Hugh-rymcu/BigSmart-Open/site/pnpm-lock.yaml

lockfileVersion: '9.0'

settings:
  autoInstallPeers: true
  excludeLinksFromLockfile: false

importers:

  .:
    dependencies:
      '@iconify-json/lucide':
        specifier: ^1.2.106
        version: 1.2.106
      '@iconify-json/simple-icons':
        specifier: ^1.2.81
        version: 1.2.81
      '@iconify-json/vscode-icons':
        specifier: ^1.2.49
        version: 1.2.49
      '@nuxt/content':
        specifier: ^3.13.0
        version: 3.13.0(better-sqlite3@12.9.0)(magicast@0.5.2)
      '@nuxt/image':
        specifier: ^2.0.0
        version: 2.0.0(db0@0.3.4(better-sqlite3@12.9.0))(ioredis@5.10.1)(magicast@0.5.2)
      '@nuxt/ui':
        specifier: ^4.7.1
        version: 4.7.1(@internationalized/date@3.12.0)(@internationalized/number@3.6.5)(@nuxt/content@3.13.0(better-sqlite3@12.9.0)(magicast@0.5.2))(@tiptap/extensions@3.22.4(@tiptap/core@3.22.4(@tiptap/pm@3.22.4))(@tiptap/pm@3.22.4))(@tiptap/y-tiptap@3.0.2(prosemirror-model@1.25.4)(prosemirror-state@1.4.4)(prosemirror-view@1.41.6)(y-protocols@1.0.7(yjs@13.6.30))(yjs@13.6.30))(change-case@5.4.4)(db0@0.3.4(better-sqlite3@12.9.0))(embla-carousel@8.6.0)(ioredis@5.10.1)(magicast@0.5.2)(tailwindcss@4.3.0)(typescript@6.0.3)(vite@7.3.2(@types/node@25.5.0)(jiti@2.6.1)(lightningcss@1.32.0)(terser@5.46.1)(yaml@2.8.2))(vue-router@5.0.6(@vue/compiler-sfc@3.5.33)(vue@3.5.33(typescript@6.0.3)))(vue@3.5.33(typescript@6.0.3))(yjs@13.6.30)(zod@4.4.3)
      '@nuxtjs/mcp-toolkit':
        specifier: ^0.16.1
        version: 0.16.1(@vue/compiler-sfc@3.5.33)(h3@1.15.11)(magicast@0.5.2)(rollup@4.60.2)(vite@7.3.2(@types/node@25.5.0)(jiti@2.6.1)(lightningcss@1.32.0)(terser@5.46.1)(yaml@2.8.2))(vue@3.5.33(typescript@6.0.3))(zod@4.4.3)
      '@nuxtjs/mdc':
        specifier: ^0.21.1
        version: 0.21.1(magicast@0.5.2)
      '@vueuse/core':
        specifier: ^14.3.0
        version: 14.3.0(vue@3.5.33(typescript@6.0.3))
      minimark:
        specifier: ^0.2.0
        version: 0.2.0
      nuxt:
        specifier: ^4.4.5
        version: 4.4.5(@babel/core@7.29.0)(@babel/plugin-syntax-jsx@7.28.6(@babel/core@7.29.0))(@parcel/watcher@2.5.6)(@types/node@25.5.0)(@vue/compiler-sfc@3.5.33)(better-sqlite3@12.9.0)(cac@6.7.14)(db0@0.3.4(better-sqlite3@12.9.0))(eslint@10.3.0(jiti@2.6.1))(ioredis@5.10.1)(lightningcss@1.32.0)(magicast@0.5.2)(optionator@0.9.4)(rollup-plugin-visualizer@7.0.1(rollup@4.60.2))(rollup@4.60.2)(terser@5.46.1)(typescript@6.0.3)(vite@7.3.2(@types/node@25.5.0)(jiti@2.6.1)(lightningcss@1.32.0)(terser@5.46.1)(yaml@2.8.2))(vue-tsc@3.2.8(typescript@6.0.3))(yaml@2.8.2)
      nuxt-llms:
        specifier: 0.2.0
        version: 0.2.0(magicast@0.5.2)
      tailwindcss:
        specifier: ^4.3.0
        version: 4.3.0
      ufo:
        specifier: ^1.6.4
        version: 1.6.4
      unist-util-visit:
        specifier: ^5.1.0
        version: 5.1.0
      zod:
        specifier: ^4.4.3
        version: 4.4.3
    devDependencies:
      '@nuxt/eslint':
        specifier: ^1.15.2
        version: 1.15.2(@typescript-eslint/utils@8.57.0(eslint@10.3.0(jiti@2.6.1))(typescript@6.0.3))(@vue/compiler-sfc@3.5.33)(eslint@10.3.0(jiti@2.6.1))(magicast@0.5.2)(typescript@6.0.3)(vite@7.3.2(@types/node@25.5.0)(jiti@2.6.1)(lightningcss@1.32.0)(terser@5.46.1)(yaml@2.8.2))
      eslint:
        specifier: ^10.3.0
        version: 10.3.0(jiti@2.6.1)
      typescript:
        specifier: ^6.0.3
        version: 6.0.3
      vue-tsc:
        specifier: ^3.2.8
        version: 3.2.8(typescript@6.0.3)

packages:

  '@alloc/quick-lru@5.2.0':
    resolution: {integrity: sha512-UrcABB+4bUrFABwbluTIBErXwvbsU/V7TZWfmbgJfbkwiBuziS9gxdODUyuiecfdGQ85jglMW6juS3+z5TsKLw==}
    engines: {node: '>=10'}

  '@antfu/install-pkg@1.1.0':
    resolution: {integrity: sha512-MGQsmw10ZyI+EJo45CdSER4zEb+p31LpDAFp2Z3gkSd1yqVZGi0Ebx++YTEMonJy4oChEMLsxZ64j8FH6sSqtQ==}

  '@apidevtools/json-schema-ref-parser@14.2.1':
    resolution: {integrity: sha512-HmdFw9CDYqM6B25pqGBpNeLCKvGPlIx1EbLrVL0zPvj50CJQUHyBNBw45Muk0kEIkogo1VZvOKHajdMuAzSxRg==}
    engines: {node: '>= 20'}
    peerDependencies:
      '@types/json-schema': ^7.0.15

  '@babel/code-frame@7.29.0':
    resolution: {integrity: sha512-9NhCeYjq9+3uxgdtp20LSiJXJvN0FeCtNGpJxuMFZ1Kv3cWUNb6DOhJwUvcVCzKGR66cw4njwM6hrJLqgOwbcw==}
    engines: {node: '>=6.9.0'}

  '@babel/compat-data@7.29.0':
    resolution: {integrity: sha512-T1NCJqT/j9+cn8fvkt7jtwbLBfLC/1y1c7NtCeXFRgzGTsafi68MRv8yzkYSapBnFA6L3U2VSc02ciDzoAJhJg==}
    engines: {node: '>=6.9.0'}

  '@babel/core@7.29.0':
    resolution: {integrity: sha512-CGOfOJqWjg2qW/Mb6zNsDm+u5vFQ8DxXfbM09z69p5Z6+mE1ikP2jUXw+j42Pf1XTYED2Rni5f95npYeuwMDQA==}
    engines: {node: '>=6.9.0'}

  '@babel/generator@7.29.1':
    resolution: {integrity: sha512-qsaF+9Qcm2Qv8SRIMMscAvG4O3lJ0F1GuMo5HR/Bp02LopNgnZBC/EkbevHFeGs4ls/oPz9v+Bsmzbkbe+0dUw==}
    engines: {node: '>=6.9.0'}

  '@babel/helper-annotate-as-pure@7.27.3':
    resolution: {integrity: sha512-fXSwMQqitTGeHLBC08Eq5yXz2m37E4pJX1qAU1+2cNedz/ifv/bVXft90VeSav5nFO61EcNgwr0aJxbyPaWBPg==}
    engines: {node: '>=6.9.0'}

  '@babel/helper-compilation-targets@7.28.6':
    resolution: {integrity: sha512-JYtls3hqi15fcx5GaSNL7SCTJ2MNmjrkHXg4FSpOA/grxK8KwyZ5bubHsCq8FXCkua6xhuaaBit+3b7+VZRfcA==}
    engines: {node: '>=6.9.0'}

  '@babel/helper-create-class-features-plugin@7.28.6':
    resolution: {integrity: sha512-dTOdvsjnG3xNT9Y0AUg1wAl38y+4Rl4sf9caSQZOXdNqVn+H+HbbJ4IyyHaIqNR6SW9oJpA/RuRjsjCw2IdIow==}
    engines: {node: '>=6.9.0'}
    peerDependencies:
      '@babel/core': ^7.0.0

  '@babel/helper-globals@7.28.0':
    resolution: {integrity: sha512-+W6cISkXFa1jXsDEdYA8HeevQT/FULhxzR99pxphltZcVaugps53THCeiWA8SguxxpSp3gKPiuYfSWopkLQ4hw==}
    engines: {node: '>=6.9.0'}

  '@babel/helper-member-expression-to-functions@7.28.5':
    resolution: {integrity: sha512-cwM7SBRZcPCLgl8a7cY0soT1SptSzAlMH39vwiRpOQkJlh53r5hdHwLSCZpQdVLT39sZt+CRpNwYG4Y2v77atg==}
    engines: {node: '>=6.9.0'}

  '@babel/helper-module-imports@7.28.6':
    resolution: {integrity: sha512-l5XkZK7r7wa9LucGw9LwZyyCUscb4x37JWTPz7swwFE/0FMQAGpiWUZn8u9DzkSBWEcK25jmvubfpw2dnAMdbw==}
    engines: {node: '>=6.9.0'}

  '@babel/helper-module-transforms@7.28.6':
    resolution: {integrity: sha512-67oXFAYr2cDLDVGLXTEABjdBJZ6drElUSI7WKp70NrpyISso3plG9SAGEF6y7zbha/wOzUByWWTJvEDVNIUGcA==}
    engines: {node: '>=6.9.0'}
    peerDependencies:
      '@babel/core': ^7.0.0

  '@babel/helper-optimise-call-expression@7.27.1':
    resolution: {integrity: sha512-URMGH08NzYFhubNSGJrpUEphGKQwMQYBySzat5cAByY1/YgIRkULnIy3tAMeszlL/so2HbeilYloUmSpd7GdVw==}
    engines: {node: '>=6.9.0'}

  '@babel/helper-plugin-utils@7.28.6':
    resolution: {integrity: sha512-S9gzZ/bz83GRysI7gAD4wPT/AI3uCnY+9xn+Mx/KPs2JwHJIz1W8PZkg2cqyt3RNOBM8ejcXhV6y8Og7ly/Dug==}
    engines: {node: '>=6.9.0'}

  '@babel/helper-replace-supers@7.28.6':
    resolution: {integrity: sha512-mq8e+laIk94/yFec3DxSjCRD2Z0TAjhVbEJY3UQrlwVo15Lmt7C2wAUbK4bjnTs4APkwsYLTahXRraQXhb1WCg==}
    engines: {node: '>=6.9.0'}
    peerDependencies:
      '@babel/core': ^7.0.0

  '@babel/helper-skip-transparent-expression-wrappers@7.27.1':
    resolution: {integrity: sha512-Tub4ZKEXqbPjXgWLl2+3JpQAYBJ8+ikpQ2Ocj/q/r0LwE3UhENh7EUabyHjz2kCEsrRY83ew2DQdHluuiDQFzg==}
    engines: {node: '>=6.9.0'}

  '@babel/helper-string-parser@7.27.1':
    resolution: {integrity: sha512-qMlSxKbpRlAridDExk92nSobyDdpPijUq2DW6oDnUqd0iOGxmQjyqhMIihI9+zv4LPyZdRje2cavWPbCbWm3eA==}
    engines: {node: '>=6.9.0'}

  '@babel/helper-validator-identifier@7.28.5':
    resolution: {integrity: sha512-qSs4ifwzKJSV39ucNjsvc6WVHs6b7S03sOh2OcHF9UHfVPqWWALUsNUVzhSBiItjRZoLHx7nIarVjqKVusUZ1Q==}
    engines: {node: '>=6.9.0'}

  '@babel/helper-validator-option@7.27.1':
    resolution: {integrity: sha512-YvjJow9FxbhFFKDSuFnVCe2WxXk1zWc22fFePVNEaWJEu8IrZVlda6N0uHwzZrUM1il7NC9Mlp4MaJYbYd9JSg==}
    engines: {node: '>=6.9.0'}

  '@babel/helpers@7.28.6':
    resolution: {integrity: sha512-xOBvwq86HHdB7WUDTfKfT/Vuxh7gElQ+Sfti2Cy6yIWNW05P8iUslOVcZ4/sKbE+/jQaukQAdz/gf3724kYdqw==}
    engines: {node: '>=6.9.0'}

  '@babel/parser@7.29.2':
    resolution: {integrity: sha512-4GgRzy/+fsBa72/RZVJmGKPmZu9Byn8o4MoLpmNe1m8ZfYnz5emHLQz3U4gLud6Zwl0RZIcgiLD7Uq7ySFuDLA==}
    engines: {node: '>=6.0.0'}
    hasBin: true

  '@babel/plugin-syntax-jsx@7.28.6':
    resolution: {integrity: sha512-wgEmr06G6sIpqr8YDwA2dSRTE3bJ+V0IfpzfSY3Lfgd7YWOaAdlykvJi13ZKBt8cZHfgH1IXN+CL656W3uUa4w==}
    engines: {node: '>=6.9.0'}
    peerDependencies:
      '@babel/core': ^7.0.0-0

  '@babel/plugin-syntax-typescript@7.28.6':
    resolution: {integrity: sha512-+nDNmQye7nlnuuHDboPbGm00Vqg3oO8niRRL27/4LYHUsHYh0zJ1xWOz0uRwNFmM1Avzk8wZbc6rdiYhomzv/A==}
    engines: {node: '>=6.9.0'}
    peerDependencies:
      '@babel/core': ^7.0.0-0

  '@babel/plugin-transform-typescript@7.28.6':
    resolution: {integrity: sha512-0YWL2RFxOqEm9Efk5PvreamxPME8OyY0wM5wh5lHjF+VtVhdneCWGzZeSqzOfiobVqQaNCd2z0tQvnI9DaPWPw==}
    engines: {node: '>=6.9.0'}
    peerDependencies:
      '@babel/core': ^7.0.0-0

  '@babel/template@7.28.6':
    resolution: {integrity: sha512-YA6Ma2KsCdGb+WC6UpBVFJGXL58MDA6oyONbjyF/+5sBgxY/dwkhLogbMT2GXXyU84/IhRw/2D1Os1B/giz+BQ==}
    engines: {node: '>=6.9.0'}

  '@babel/traverse@7.29.0':
    resolution: {integrity: sha512-4HPiQr0X7+waHfyXPZpWPfWL/J7dcN1mx9gL6WdQVMbPnF3+ZhSMs8tCxN7oHddJE9fhNE7+lxdnlyemKfJRuA==}
    engines: {node: '>=6.9.0'}

  '@babel/types@7.29.0':
    resolution: {integrity: sha512-LwdZHpScM4Qz8Xw2iKSzS+cfglZzJGvofQICy7W7v4caru4EaAmyUuO6BGrbyQ2mYV11W0U8j5mBhd14dd3B0A==}
    engines: {node: '>=6.9.0'}

  '@bomb.sh/tab@0.0.14':
    resolution: {integrity: sha512-cHMk2LI430MVoX1unTt9oK1iZzQS4CYDz97MSxKLNErW69T43Z2QLFTpdS/3jVOIKrIADWfuxQ+nQNJkNV7E4w==}
    hasBin: true
    peerDependencies:
      cac: ^6.7.14
      citty: ^0.1.6 || ^0.2.0
      commander: ^13.1.0
    peerDependenciesMeta:
      cac:
        optional: true
      citty:
        optional: true
      commander:
        optional: true

  '@capsizecss/unpack@4.0.0':
    resolution: {integrity: sha512-VERIM64vtTP1C4mxQ5thVT9fK0apjPFobqybMtA1UdUujWka24ERHbRHFGmpbbhp73MhV+KSsHQH9C6uOTdEQA==}
    engines: {node: '>=18'}

  '@clack/core@1.3.0':
    resolution: {integrity: sha512-xJPHpAmEQUBrXSLx0gF+q5K/IyihXpsHZcha+jB+tyahsKRK3Dxo4D0coZDewHo12NhiuzC3dTtMPbm53GEAAA==}
    engines: {node: '>= 20.12.0'}

  '@clack/prompts@1.3.0':
    resolution: {integrity: sha512-GgcWwRCs/xPtaqlMy8qRhPnZf9vlWcWZNHAitnVQ3yk7JmSralSiq5q07yaffYE8SogtDm7zFeKccx1QNVARpw==}
    engines: {node: '>= 20.12.0'}

  '@cloudflare/kv-asset-handler@0.4.2':
    resolution: {integrity: sha512-SIOD2DxrRRwQ+jgzlXCqoEFiKOFqaPjhnNTGKXSRLvp1HiOvapLaFG2kEr9dYQTYe8rKrd9uvDUzmAITeNyaHQ==}
    engines: {node: '>=18.0.0'}

  '@colordx/core@5.4.3':
    resolution: {integrity: sha512-kIxYSfA5T8HXjav55UaaH/o/cKivF6jCCGIb8eqtcsfI46wsvlSiT8jMDyrl779qLec3c2c2oHBZo4oAhvbjrQ==}

  '@dxup/nuxt@0.4.1':
    resolution: {integrity: sha512-gtYffW6OfWNvoLW+XD3Mx/K8uUq08PMGLYJoDxc92EzZAWqR0FhcR5iaLm5r/OxyGTKz+P5f5Y7Aoir9+SjYaw==}
    peerDependencies:
      typescript: '*'
    peerDependenciesMeta:
      typescript:
        optional: true

  '@dxup/unimport@0.1.2':
    resolution: {integrity: sha512-/B8YJGPzaYq1NbsQmwgP8EZqg40NpTw4ZB3suuI0TplbxKHeK94jeaawLmVhCv+YwUnOpiWEz9U6SeThku/8JQ==}

  '@emnapi/core@1.10.0':
    resolution: {integrity: sha512-yq6OkJ4p82CAfPl0u9mQebQHKPJkY7WrIuk205cTYnYe+k2Z8YBh11FrbRG/H6ihirqcacOgl2BIO8oyMQLeXw==}

  '@emnapi/runtime@1.10.0':
    resolution: {integrity: sha512-ewvYlk86xUoGI0zQRNq/mC+16R1QeDlKQy21Ki3oSYXNgLb45GV1P6A0M+/s6nyCuNDqe5VpaY84BzXGwVbwFA==}

  '@emnapi/wasi-threads@1.2.1':
    resolution: {integrity: sha512-uTII7OYF+/Mes/MrcIOYp5yOtSMLBWSIoLPpcgwipoiKbli6k322tcoFsxoIIxPDqW01SQGAgko4EzZi2BNv2w==}

  '@es-joy/jsdoccomment@0.84.0':
    resolution: {integrity: sha512-0xew1CxOam0gV5OMjh2KjFQZsKL2bByX1+q4j3E73MpYIdyUxcZb/xQct9ccUb+ve5KGUYbCUxyPnYB7RbuP+w==}
    engines: {node: ^20.19.0 || ^22.13.0 || >=24}

  '@es-joy/resolve.exports@1.2.0':
    resolution: {integrity: sha512-Q9hjxWI5xBM+qW2enxfe8wDKdFWMfd0Z29k5ZJnuBqD/CasY5Zryj09aCA6owbGATWz+39p5uIdaHXpopOcG8g==}
    engines: {node: '>=10'}

  '@esbuild/aix-ppc64@0.27.4':
    resolution: {integrity: sha512-cQPwL2mp2nSmHHJlCyoXgHGhbEPMrEEU5xhkcy3Hs/O7nGZqEpZ2sUtLaL9MORLtDfRvVl2/3PAuEkYZH0Ty8Q==}
    engines: {node: '>=18'}
    cpu: [ppc64]
    os: [aix]

  '@esbuild/aix-ppc64@0.28.0':
    resolution: {integrity: sha512-lhRUCeuOyJQURhTxl4WkpFTjIsbDayJHih5kZC1giwE+MhIzAb7mEsQMqMf18rHLsrb5qI1tafG20mLxEWcWlA==}
    engines: {node: '>=18'}
    cpu: [ppc64]
    os: [aix]

  '@esbuild/android-arm64@0.27.4':
    resolution: {integrity: sha512-gdLscB7v75wRfu7QSm/zg6Rx29VLdy9eTr2t44sfTW7CxwAtQghZ4ZnqHk3/ogz7xao0QAgrkradbBzcqFPasw==}
    engines: {node: '>=18'}
    cpu: [arm64]
    os: [android]

  '@esbuild/android-arm64@0.28.0':
    resolution: {integrity: sha512-+WzIXQOSaGs33tLEgYPYe/yQHf0WTU0X42Jca3y8NWMbUVhp7rUnw+vAsRC/QiDrdD31IszMrZy+qwPOPjd+rw==}
    engines: {node: '>=18'}
    cpu: [arm64]
    os: [android]

  '@esbuild/android-arm@0.27.4':
    resolution: {integrity: sha512-X9bUgvxiC8CHAGKYufLIHGXPJWnr0OCdR0anD2e21vdvgCI8lIfqFbnoeOz7lBjdrAGUhqLZLcQo6MLhTO2DKQ==}
    engines: {node: '>=18'}
    cpu: [arm]
    os: [android]

  '@esbuild/android-arm@0.28.0':
    resolution: {integrity: sha512-wqh0ByljabXLKHeWXYLqoJ5jKC4XBaw6Hk08OfMrCRd2nP2ZQ5eleDZC41XHyCNgktBGYMbqnrJKq/K/lzPMSQ==}
    engines: {node: '>=18'}
    cpu: [arm]
    os: [android]

  '@esbuild/android-x64@0.27.4':
    resolution: {integrity: sha512-PzPFnBNVF292sfpfhiyiXCGSn9HZg5BcAz+ivBuSsl6Rk4ga1oEXAamhOXRFyMcjwr2DVtm40G65N3GLeH1Lvw==}
    engines: {node: '>=18'}
    cpu: [x64]
    os: [android]

  '@esbuild/android-x64@0.28.0':
    resolution: {integrity: sha512-+VJggoaKhk2VNNqVL7f6S189UzShHC/mR9EE8rDdSkdpN0KflSwWY/gWjDrNxxisg8Fp1ZCD9jLMo4m0OUfeUA==}
    engines: {node: '>=18'}
    cpu: [x64]
    os: [android]

  '@esbuild/darwin-arm64@0.27.4':
    resolution: {integrity: sha512-b7xaGIwdJlht8ZFCvMkpDN6uiSmnxxK56N2GDTMYPr2/gzvfdQN8rTfBsvVKmIVY/X7EM+/hJKEIbbHs9oA4tQ==}
    engines: {node: '>=18'}
    cpu: [arm64]
    os: [darwin]

  '@esbuild/darwin-arm64@0.28.0':
    resolution: {integrity: sha512-0T+A9WZm+bZ84nZBtk1ckYsOvyA3x7e2Acj1KdVfV4/2tdG4fzUp91YHx+GArWLtwqp77pBXVCPn2We7Letr0Q==}
    engines: {node: '>=18'}
    cpu: [arm64]
    os: [darwin]

  '@esbuild/darwin-x64@0.27.4':
    resolution: {integrity: sha512-sR+OiKLwd15nmCdqpXMnuJ9W2kpy0KigzqScqHI3Hqwr7IXxBp3Yva+yJwoqh7rE8V77tdoheRYataNKL4QrPw==}
    engines: {node: '>=18'}
    cpu: [x64]
    os: [darwin]

  '@esbuild/darwin-x64@0.28.0':
    resolution: {integrity: sha512-fyzLm/DLDl/84OCfp2f/XQ4flmORsjU7VKt8HLjvIXChJoFFOIL6pLJPH4Yhd1n1gGFF9mPwtlN5Wf82DZs+LQ==}
    engines: {node: '>=18'}
    cpu: [x64]
    os: [darwin]

  '@esbuild/freebsd-arm64@0.27.4':
    resolution: {integrity: sha512-jnfpKe+p79tCnm4GVav68A7tUFeKQwQyLgESwEAUzyxk/TJr4QdGog9sqWNcUbr/bZt/O/HXouspuQDd9JxFSw==}
    engines: {node: '>=18'}
    cpu: [arm64]
    os: [freebsd]

  '@esbuild/freebsd-arm64@0.28.0':
    resolution: {integrity: sha512-l9GeW5UZBT9k9brBYI+0WDffcRxgHQD8ShN2Ur4xWq/NFzUKm3k5lsH4PdaRgb2w7mI9u61nr2gI2mLI27Nh3Q==}
    engines: {node: '>=18'}
    cpu: [arm64]
    os: [freebsd]

  '@esbuild/freebsd-x64@0.27.4':
    resolution: {integrity: sha512-2kb4ceA/CpfUrIcTUl1wrP/9ad9Atrp5J94Lq69w7UwOMolPIGrfLSvAKJp0RTvkPPyn6CIWrNy13kyLikZRZQ==}
    engines: {node: '>=18'}
    cpu: [x64]
    os: [freebsd]

  '@esbuild/freebsd-x64@0.28.0':
    resolution: {integrity: sha512-BXoQai/A0wPO6Es3yFJ7APCiKGc1tdAEOgeTNy3SsB491S3aHn4S4r3e976eUnPdU+NbdtmBuLncYir2tMU9Nw==}
    engines: {node: '>=18'}
    cpu: [x64]
    os: [freebsd]

  '@esbuild/linux-arm64@0.27.4':
    resolution: {integrity: sha512-7nQOttdzVGth1iz57kxg9uCz57dxQLHWxopL6mYuYthohPKEK0vU0C3O21CcBK6KDlkYVcnDXY099HcCDXd9dA==}
    engines: {node: '>=18'}
    cpu: [arm64]
    os: [linux]

  '@esbuild/linux-arm64@0.28.0':
    resolution: {integrity: sha512-RVyzfb3FWsGA55n6WY0MEIEPURL1FcbhFE6BffZEMEekfCzCIMtB5yyDcFnVbTnwk+CLAgTujmV/Lgvih56W+A==}
    engines: {node: '>=18'}
    cpu: [arm64]
    os: [linux]

  '@esbuild/linux-arm@0.27.4':
    resolution: {integrity: sha512-aBYgcIxX/wd5n2ys0yESGeYMGF+pv6g0DhZr3G1ZG4jMfruU9Tl1i2Z+Wnj9/KjGz1lTLCcorqE2viePZqj4Eg==}
    engines: {node: '>=18'}
    cpu: [arm]
    os: [linux]

  '@esbuild/linux-arm@0.28.0':
    resolution: {integrity: sha512-CjaaREJagqJp7iTaNQjjidaNbCKYcd4IDkzbwwxtSvjI7NZm79qiHc8HqciMddQ6CKvJT6aBd8lO9kN/ZudLlw==}
    engines: {node: '>=18'}
    cpu: [arm]
    os: [linux]

  '@esbuild/linux-ia32@0.27.4':
    resolution: {integrity: sha512-oPtixtAIzgvzYcKBQM/qZ3R+9TEUd1aNJQu0HhGyqtx6oS7qTpvjheIWBbes4+qu1bNlo2V4cbkISr8q6gRBFA==}
    engines: {node: '>=18'}
    cpu: [ia32]
    os: [linux]

  '@esbuild/linux-ia32@0.28.0':
    resolution: {integrity: sha512-KBnSTt1kxl9x70q+ydterVdl+Cn0H18ngRMRCEQfrbqdUuntQQ0LoMZv47uB97NljZFzY6HcfqEZ2SAyIUTQBQ==}
    engines: {node: '>=18'}
    cpu: [ia32]
    os: [linux]

  '@esbuild/linux-loong64@0.27.4':
    resolution: {integrity: sha512-8mL/vh8qeCoRcFH2nM8wm5uJP+ZcVYGGayMavi8GmRJjuI3g1v6Z7Ni0JJKAJW+m0EtUuARb6Lmp4hMjzCBWzA==}
    engines: {node: '>=18'}
    cpu: [loong64]
    os: [linux]

  '@esbuild/linux-loong64@0.28.0':
    resolution: {integrity: sha512-zpSlUce1mnxzgBADvxKXX5sl8aYQHo2ezvMNI8I0lbblJtp8V4odlm3Yzlj7gPyt3T8ReksE6bK+pT3WD+aJRg==}
    engines: {node: '>=18'}
    cpu: [loong64]
    os: [linux]

  '@esbuild/linux-mips64el@0.27.4':
    resolution: {integrity: sha512-1RdrWFFiiLIW7LQq9Q2NES+HiD4NyT8Itj9AUeCl0IVCA459WnPhREKgwrpaIfTOe+/2rdntisegiPWn/r/aAw==}
    engines: {node: '>=18'}
    cpu: [mips64el]
    os: [linux]

  '@esbuild/linux-mips64el@0.28.0':
    resolution: {integrity: sha512-2jIfP6mmjkdmeTlsX/9vmdmhBmKADrWqN7zcdtHIeNSCH1SqIoNI63cYsjQR8J+wGa4Y5izRcSHSm8K3QWmk3w==}
    engines: {node: '>=18'}
    cpu: [mips64el]
    os: [linux]

  '@esbuild/linux-ppc64@0.27.4':
    resolution: {integrity: sha512-tLCwNG47l3sd9lpfyx9LAGEGItCUeRCWeAx6x2Jmbav65nAwoPXfewtAdtbtit/pJFLUWOhpv0FpS6GQAmPrHA==}
    engines: {node: '>=18'}
    cpu: [ppc64]
    os: [linux]

  '@esbuild/linux-ppc64@0.28.0':
    resolution: {integrity: sha512-bc0FE9wWeC0WBm49IQMPSPILRocGTQt3j5KPCA8os6VprfuJ7KD+5PzESSrJ6GmPIPJK965ZJHTUlSA6GNYEhg==}
    engines: {node: '>=18'}
    cpu: [ppc64]
    os: [linux]

  '@esbuild/linux-riscv64@0.27.4':
    resolution: {integrity: sha512-BnASypppbUWyqjd1KIpU4AUBiIhVr6YlHx/cnPgqEkNoVOhHg+YiSVxM1RLfiy4t9cAulbRGTNCKOcqHrEQLIw==}
    engines: {node: '>=18'}
    cpu: [riscv64]
    os: [linux]

  '@esbuild/linux-riscv64@0.28.0':
    resolution: {integrity: sha512-SQPZOwoTTT/HXFXQJG/vBX8sOFagGqvZyXcgLA3NhIqcBv1BJU1d46c0rGcrij2B56Z2rNiSLaZOYW5cUk7yLQ==}
    engines: {node: '>=18'}
    cpu: [riscv64]
    os: [linux]

  '@esbuild/linux-s390x@0.27.4':
    resolution: {integrity: sha512-+eUqgb/Z7vxVLezG8bVB9SfBie89gMueS+I0xYh2tJdw3vqA/0ImZJ2ROeWwVJN59ihBeZ7Tu92dF/5dy5FttA==}
    engines: {node: '>=18'}
    cpu: [s390x]
    os: [linux]

  '@esbuild/linux-s390x@0.28.0':
    resolution: {integrity: sha512-SCfR0HN8CEEjnYnySJTd2cw0k9OHB/YFzt5zgJEwa+wL/T/raGWYMBqwDNAC6dqFKmJYZoQBRfHjgwLHGSrn3Q==}
    engines: {node: '>=18'}
    cpu: [s390x]
    os: [linux]

  '@esbuild/linux-x64@0.27.4':
    resolution: {integrity: sha512-S5qOXrKV8BQEzJPVxAwnryi2+Iq5pB40gTEIT69BQONqR7JH1EPIcQ/Uiv9mCnn05jff9umq/5nqzxlqTOg9NA==}
    engines: {node: '>=18'}
    cpu: [x64]
    os: [linux]

  '@esbuild/linux-x64@0.28.0':
    resolution: {integrity: sha512-us0dSb9iFxIi8srnpl931Nvs65it/Jd2a2K3qs7fz2WfGPHqzfzZTfec7oxZJRNPXPnNYZtanmRc4AL/JwVzHQ==}
    engines: {node: '>=18'}
    cpu: [x64]
    os: [linux]

  '@esbuild/netbsd-arm64@0.27.4':
    resolution: {integrity: sha512-xHT8X4sb0GS8qTqiwzHqpY00C95DPAq7nAwX35Ie/s+LO9830hrMd3oX0ZMKLvy7vsonee73x0lmcdOVXFzd6Q==}
    engines: {node: '>=18'}
    cpu: [arm64]
    os: [netbsd]

  '@esbuild/netbsd-arm64@0.28.0':
    resolution: {integrity: sha512-CR/RYotgtCKwtftMwJlUU7xCVNg3lMYZ0RzTmAHSfLCXw3NtZtNpswLEj/Kkf6kEL3Gw+BpOekRX0BYCtklhUw==}
    engines: {node: '>=18'}
    cpu: [arm64]
    os: [netbsd]

  '@esbuild/netbsd-x64@0.27.4':
    resolution: {integrity: sha512-RugOvOdXfdyi5Tyv40kgQnI0byv66BFgAqjdgtAKqHoZTbTF2QqfQrFwa7cHEORJf6X2ht+l9ABLMP0dnKYsgg==}
    engines: {node: '>=18'}
    cpu: [x64]
    os: [netbsd]

  '@esbuild/netbsd-x64@0.28.0':
    resolution: {integrity: sha512-nU1yhmYutL+fQ71Kxnhg8uEOdC0pwEW9entHykTgEbna2pw2dkbFSMeqjjyHZoCmt8SBkOSvV+yNmm94aUrrqw==}
    engines: {node: '>=18'}
    cpu: [x64]
    os: [netbsd]

  '@esbuild/openbsd-arm64@0.27.4':
    resolution: {integrity: sha512-2MyL3IAaTX+1/qP0O1SwskwcwCoOI4kV2IBX1xYnDDqthmq5ArrW94qSIKCAuRraMgPOmG0RDTA74mzYNQA9ow==}
    engines: {node: '>=18'}
    cpu: [arm64]
    os: [openbsd]

  '@esbuild/openbsd-arm64@0.28.0':
    resolution: {integrity: sha512-cXb5vApOsRsxsEl4mcZ1XY3D4DzcoMxR/nnc4IyqYs0rTI8ZKmW6kyyg+11Z8yvgMfAEldKzP7AdP64HnSC/6g==}
    engines: {node: '>=18'}
    cpu: [arm64]
    os: [openbsd]

  '@esbuild/openbsd-x64@0.27.4':
    resolution: {integrity: sha512-u8fg/jQ5aQDfsnIV6+KwLOf1CmJnfu1ShpwqdwC0uA7ZPwFws55Ngc12vBdeUdnuWoQYx/SOQLGDcdlfXhYmXQ==}
    engines: {node: '>=18'}
    cpu: [x64]
    os: [openbsd]

  '@esbuild/openbsd-x64@0.28.0':
    resolution: {integrity: sha512-8wZM2qqtv9UP3mzy7HiGYNH/zjTA355mpeuA+859TyR+e+Tc08IHYpLJuMsfpDJwoLo1ikIJI8jC3GFjnRClzA==}
    engines: {node: '>=18'}
    cpu: [x64]
    os: [openbsd]

  '@esbuild/openharmony-arm64@0.27.4':
    resolution: {integrity: sha512-JkTZrl6VbyO8lDQO3yv26nNr2RM2yZzNrNHEsj9bm6dOwwu9OYN28CjzZkH57bh4w0I2F7IodpQvUAEd1mbWXg==}
    engines: {node: '>=18'}
    cpu: [arm64]
    os: [openharmony]

  '@esbuild/openharmony-arm64@0.28.0':
    resolution: {integrity: sha512-FLGfyizszcef5C3YtoyQDACyg95+dndv79i2EekILBofh5wpCa1KuBqOWKrEHZg3zrL3t5ouE5jgr94vA+Wb2w==}
    engines: {node: '>=18'}
    cpu: [arm64]
    os: [openharmony]

  '@esbuild/sunos-x64@0.27.4':
    resolution: {integrity: sha512-/gOzgaewZJfeJTlsWhvUEmUG4tWEY2Spp5M20INYRg2ZKl9QPO3QEEgPeRtLjEWSW8FilRNacPOg8R1uaYkA6g==}
    engines: {node: '>=18'}
    cpu: [x64]
    os: [sunos]

  '@esbuild/sunos-x64@0.28.0':
    resolution: {integrity: sha512-1ZgjUoEdHZZl/YlV76TSCz9Hqj9h9YmMGAgAPYd+q4SicWNX3G5GCyx9uhQWSLcbvPW8Ni7lj4gDa1T40akdlw==}
    engines: {node: '>=18'}
    cpu: [x64]
    os: [sunos]

  '@esbuild/win32-arm64@0.27.4':
    resolution: {integrity: sha512-Z9SExBg2y32smoDQdf1HRwHRt6vAHLXcxD2uGgO/v2jK7Y718Ix4ndsbNMU/+1Qiem9OiOdaqitioZwxivhXYg==}
    engines: {node: '>=18'}
    cpu: [arm64]
    os: [win32]

  '@esbuild/win32-arm64@0.28.0':
    resolution: {integrity: sha512-Q9StnDmQ/enxnpxCCLSg0oo4+34B9TdXpuyPeTedN/6+iXBJ4J+zwfQI28u/Jl40nOYAxGoNi7mFP40RUtkmUA==}
    engines: {node: '>=18'}
    cpu: [arm64]
    os: [win32]

  '@esbuild/win32-ia32@0.27.4':
    resolution: {integrity: sha512-DAyGLS0Jz5G5iixEbMHi5KdiApqHBWMGzTtMiJ72ZOLhbu/bzxgAe8Ue8CTS3n3HbIUHQz/L51yMdGMeoxXNJw==}
    engines: {node: '>=18'}
    cpu: [ia32]
    os: [win32]

  '@esbuild/win32-ia32@0.28.0':
    resolution: {integrity: sha512-zF3ag/gfiCe6U2iczcRzSYJKH1DCI+ByzSENHlM2FcDbEeo5Zd2C86Aq0tKUYAJJ1obRP84ymxIAksZUcdztHA==}
    engines: {node: '>=18'}
    cpu: [ia32]
    os: [win32]

  '@esbuild/win32-x64@0.27.4':
    resolution: {integrity: sha512-+knoa0BDoeXgkNvvV1vvbZX4+hizelrkwmGJBdT17t8FNPwG2lKemmuMZlmaNQ3ws3DKKCxpb4zRZEIp3UxFCg==}
    engines: {node: '>=18'}
    cpu: [x64]
    os: [win32]

  '@esbuild/win32-x64@0.28.0':
    resolution: {integrity: sha512-pEl1bO9mfAmIC+tW5btTmrKaujg3zGtUmWNdCw/xs70FBjwAL3o9OEKNHvNmnyylD6ubxUERiEhdsL0xBQ9efw==}
    engines: {node: '>=18'}
    cpu: [x64]
    os: [win32]

  '@eslint-community/eslint-utils@4.9.1':
    resolution: {integrity: sha512-phrYmNiYppR7znFEdqgfWHXR6NCkZEK7hwWDHZUjit/2/U0r6XvkDl0SYnoM51Hq7FhCGdLDT6zxCCOY1hexsQ==}
    engines: {node: ^12.22.0 || ^14.17.0 || >=16.0.0}
    peerDependencies:
      eslint: ^6.0.0 || ^7.0.0 || >=8.0.0

  '@eslint-community/regexpp@4.12.2':
    resolution: {integrity: sha512-EriSTlt5OC9/7SXkRSCAhfSxxoSUgBm33OH+IkwbdpgoqsSsUg7y3uh+IICI/Qg4BBWr3U2i39RpmycbxMq4ew==}
    engines: {node: ^12.0.0 || ^14.0.0 || >=16.0.0}

  '@eslint/compat@2.0.3':
    resolution: {integrity: sha512-SjIJhGigp8hmd1YGIBwh7Ovri7Kisl42GYFjrOyHhtfYGGoLW6teYi/5p8W50KSsawUPpuLOSmsq1bD0NGQLBw==}
    engines: {node: ^20.19.0 || ^22.13.0 || >=24}
    peerDependencies:
      eslint: ^8.40 || 9 || 10
    peerDependenciesMeta:
      eslint:
        optional: true

  '@eslint/config-array@0.23.5':
    resolution: {integrity: sha512-Y3kKLvC1dvTOT+oGlqNQ1XLqK6D1HU2YXPc52NmAlJZbMMWDzGYXMiPRJ8TYD39muD/OTjlZmNJ4ib7dvSrMBA==}
    engines: {node: ^20.19.0 || ^22.13.0 || >=24}

  '@eslint/config-helpers@0.5.5':
    resolution: {integrity: sha512-eIJYKTCECbP/nsKaaruF6LW967mtbQbsw4JTtSVkUQc9MneSkbrgPJAbKl9nWr0ZeowV8BfsarBmPpBzGelA2w==}
    engines: {node: ^20.19.0 || ^22.13.0 || >=24}

  '@eslint/config-inspector@1.5.0':
    resolution: {integrity: sha512-YK/VdQ+pibx5pcCI2GPZVO6vFemf/pkB662HuFtc5AA4WLQ9upb3fAoZSjOAYoDJx58qGTDp6xq9ldd/vluNxQ==}
    hasBin: true
    peerDependencies:
      eslint: ^8.50.0 || ^9.0.0 || ^10.0.0

  '@eslint/core@1.2.1':
    resolution: {integrity: sha512-MwcE1P+AZ4C6DWlpin/OmOA54mmIZ/+xZuJiQd4SyB29oAJjN30UW9wkKNptW2ctp4cEsvhlLY/CsQ1uoHDloQ==}
    engines: {node: ^20.19.0 || ^22.13.0 || >=24}

  '@eslint/js@9.39.4':
    resolution: {integrity: sha512-nE7DEIchvtiFTwBw4Lfbu59PG+kCofhjsKaCWzxTpt4lfRjRMqG6uMBzKXuEcyXhOHoUp9riAm7/aWYGhXZ9cw==}
    engines: {node: ^18.18.0 || ^20.9.0 || >=21.1.0}

  '@eslint/object-schema@3.0.5':
    resolution: {integrity: sha512-vqTaUEgxzm+YDSdElad6PiRoX4t8VGDjCtt05zn4nU810UIx/uNEV7/lZJ6KwFThKZOzOxzXy48da+No7HZaMw==}
    engines: {node: ^20.19.0 || ^22.13.0 || >=24}

  '@eslint/plugin-kit@0.7.1':
    resolution: {integrity: sha512-rZAP3aVgB9ds9KOeUSL+zZ21hPmo8dh6fnIFwRQj5EAZl9gzR7wxYbYXYysAM8CTqGmUGyp2S4kUdV17MnGuWQ==}
    engines: {node: ^20.19.0 || ^22.13.0 || >=24}

  '@fastify/accept-negotiator@2.0.1':
    resolution: {integrity: sha512-/c/TW2bO/v9JeEgoD/g1G5GxGeCF1Hafdf79WPmUlgYiBXummY0oX3VVq4yFkKKVBKDNlaDUYoab7g38RpPqCQ==}

  '@floating-ui/core@1.7.5':
    resolution: {integrity: sha512-1Ih4WTWyw0+lKyFMcBHGbb5U5FtuHJuujoyyr5zTaWS5EYMeT6Jb2AuDeftsCsEuchO+mM2ij5+q9crhydzLhQ==}

  '@floating-ui/dom@1.7.6':
    resolution: {integrity: sha512-9gZSAI5XM36880PPMm//9dfiEngYoC6Am2izES1FF406YFsjvyBMmeJ2g4SAju3xWwtuynNRFL2s9hgxpLI5SQ==}

  '@floating-ui/utils@0.2.11':
    resolution: {integrity: sha512-RiB/yIh78pcIxl6lLMG0CgBXAZ2Y0eVHqMPYugu+9U0AeT6YBeiJpf7lbdJNIugFP5SIjwNRgo4DhR1Qxi26Gg==}

  '@floating-ui/vue@1.1.11':
    resolution: {integrity: sha512-HzHKCNVxnGS35r9fCHBc3+uCnjw9IWIlCPL683cGgM9Kgj2BiAl8x1mS7vtvP6F9S/e/q4O6MApwSHj8hNLGfw==}

  '@hono/node-server@1.19.11':
    resolution: {integrity: sha512-dr8/3zEaB+p0D2n/IUrlPF1HZm586qgJNXK1a9fhg/PzdtkK7Ksd5l312tJX2yBuALqDYBlG20QEbayqPyxn+g==}
    engines: {node: '>=18.14.1'}
    peerDependencies:
      hono: ^4

  '@humanfs/core@0.19.1':
    resolution: {integrity: sha512-5DyQ4+1JEUzejeK1JGICcideyfUbGixgS9jNgex5nqkW+cY7WZhxBigmieN5Qnw9ZosSNVC9KQKyb+GUaGyKUA==}
    engines: {node: '>=18.18.0'}

  '@humanfs/node@0.16.7':
    resolution: {integrity: sha512-/zUx+yOsIrG4Y43Eh2peDeKCxlRt/gET6aHfaKpuq267qXdYDFViVHfMaLyygZOnl0kGWxFIgsBy8QFuTLUXEQ==}
    engines: {node: '>=18.18.0'}

  '@humanwhocodes/module-importer@1.0.1':
    resolution: {integrity: sha512-bxveV4V8v5Yb4ncFTT3rPSgZBOpCkjfK0y4oVVVJwIuDVBRMDXrPyXRL988i5ap9m9bnyEEjWfm5WkBmtffLfA==}
    engines: {node: '>=12.22'}

  '@humanwhocodes/retry@0.4.3':
    resolution: {integrity: sha512-bV0Tgo9K4hfPCek+aMAn81RppFKv2ySDQeMoSZuvTASywNTnVJCArCZE2FWqpvIatKu7VMRLWlR1EazvVhDyhQ==}
    engines: {node: '>=18.18'}

  '@iconify-json/lucide@1.2.106':
    resolution: {integrity: sha512-5nuejHR29A0iQjvLZRRPtuMyj1DA9pzcDMuHD4vmhG7GgLen8haMKiZcZ1IpKVZDwR8wxfcbCv9MsoWHBBAa+g==}

  '@iconify-json/simple-icons@1.2.81':
    resolution: {integrity: sha512-Utjw4sPtoVdbpAQAkC4O0cYpt4ehQZYr6aFHhmvdeW8mQwkINyAe0ogTPqNptSSKogZ2lfgXM8zpuhO961Wnng==}

  '@iconify-json/vscode-icons@1.2.49':
    resolution: {integrity: sha512-kPSF7NYMEepp/YxM/Sz9AK3+8tEb4Vz94N67OH4Xw9PetIs6at9iETVAAD47WR1sV+VkQo+Uynd8IMKw3J5NGQ==}

  '@iconify/collections@1.0.661':
    resolution: {integrity: sha512-r5dwSQHdwNxfjx8AZiHfn8IuafVYTl850xzN9gKVMi8L9sXyd/XNawTr1qIJQZbJxouCETielBRP8TM9YmiSEA==}

  '@iconify/types@2.0.0':
    resolution: {integrity: sha512-+wluvCrRhXrhyOmRDJ3q8mux9JkKy5SJ/v8ol2tu4FVjyYvtEzkc/3pK15ET6RKg4b4w4BmTk1+gsCUhf21Ykg==}

  '@iconify/utils@3.1.0':
    resolution: {integrity: sha512-Zlzem1ZXhI1iHeeERabLNzBHdOa4VhQbqAcOQaMKuTuyZCpwKbC2R4Dd0Zo3g9EAc+Y4fiarO8HIHRAth7+skw==}

  '@iconify/vue@5.0.0':
    resolution: {integrity: sha512-C+KuEWIF5nSBrobFJhT//JS87OZ++QDORB6f2q2Wm6fl2mueSTpFBeBsveK0KW9hWiZ4mNiPjsh6Zs4jjdROSg==}
    peerDependencies:
      vue: '>=3'

  '@img/colour@1.1.0':
    resolution: {integrity: sha512-Td76q7j57o/tLVdgS746cYARfSyxk8iEfRxewL9h4OMzYhbW4TAcppl0mT4eyqXddh6L/jwoM75mo7ixa/pCeQ==}
    engines: {node: '>=18'}

  '@img/sharp-darwin-arm64@0.34.5':
    resolution: {integrity: sha512-imtQ3WMJXbMY4fxb/Ndp6HBTNVtWCUI0WdobyheGf5+ad6xX8VIDO8u2xE4qc/fr08CKG/7dDseFtn6M6g/r3w==}
    engines: {node: ^18.17.0 || ^20.3.0 || >=21.0.0}
    cpu: [arm64]
    os: [darwin]

  '@img/sharp-darwin-x64@0.34.5':
    resolution: {integrity: sha512-YNEFAF/4KQ/PeW0N+r+aVVsoIY0/qxxikF2SWdp+NRkmMB7y9LBZAVqQ4yhGCm/H3H270OSykqmQMKLBhBJDEw==}
    engines: {node: ^18.17.0 || ^20.3.0 || >=21.0.0}
    cpu: [x64]
    os: [darwin]

  '@img/sharp-libvips-darwin-arm64@1.2.4':
    resolution: {integrity: sha512-zqjjo7RatFfFoP0MkQ51jfuFZBnVE2pRiaydKJ1G/rHZvnsrHAOcQALIi9sA5co5xenQdTugCvtb1cuf78Vf4g==}
    cpu: [arm64]
    os: [darwin]

  '@img/sharp-libvips-darwin-x64@1.2.4':
    resolution: {integrity: sha512-1IOd5xfVhlGwX+zXv2N93k0yMONvUlANylbJw1eTah8K/Jtpi15KC+WSiaX/nBmbm2HxRM1gZ0nSdjSsrZbGKg==}
    cpu: [x64]
    os: [darwin]

  '@img/sharp-libvips-linux-arm64@1.2.4':
    resolution: {integrity: sha512-excjX8DfsIcJ10x1Kzr4RcWe1edC9PquDRRPx3YVCvQv+U5p7Yin2s32ftzikXojb1PIFc/9Mt28/y+iRklkrw==}
    cpu: [arm64]
    os: [linux]
    libc: [glibc]

  '@img/sharp-libvips-linux-arm@1.2.4':
    resolution: {integrity: sha512-bFI7xcKFELdiNCVov8e44Ia4u2byA+l3XtsAj+Q8tfCwO6BQ8iDojYdvoPMqsKDkuoOo+X6HZA0s0q11ANMQ8A==}
    cpu: [arm]
    os: [linux]
    libc: [glibc]

  '@img/sharp-libvips-linux-ppc64@1.2.4':
    resolution: {integrity: sha512-FMuvGijLDYG6lW+b/UvyilUWu5Ayu+3r2d1S8notiGCIyYU/76eig1UfMmkZ7vwgOrzKzlQbFSuQfgm7GYUPpA==}
    cpu: [ppc64]
    os: [linux]
    libc: [glibc]

  '@img/sharp-libvips-linux-riscv64@1.2.4':
    resolution: {integrity: sha512-oVDbcR4zUC0ce82teubSm+x6ETixtKZBh/qbREIOcI3cULzDyb18Sr/Wcyx7NRQeQzOiHTNbZFF1UwPS2scyGA==}
    cpu: [riscv64]
    os: [linux]
    libc: [glibc]

  '@img/sharp-libvips-linux-s390x@1.2.4':
    resolution: {integrity: sha512-qmp9VrzgPgMoGZyPvrQHqk02uyjA0/QrTO26Tqk6l4ZV0MPWIW6LTkqOIov+J1yEu7MbFQaDpwdwJKhbJvuRxQ==}
    cpu: [s390x]
    os: [linux]
    libc: [glibc]

  '@img/sharp-libvips-linux-x64@1.2.4':
    resolution: {integrity: sha512-tJxiiLsmHc9Ax1bz3oaOYBURTXGIRDODBqhveVHonrHJ9/+k89qbLl0bcJns+e4t4rvaNBxaEZsFtSfAdquPrw==}
    cpu: [x64]
    os: [linux]
    libc: [glibc]

  '@img/sharp-libvips-linuxmusl-arm64@1.2.4':
    resolution: {integrity: sha512-FVQHuwx1IIuNow9QAbYUzJ+En8KcVm9Lk5+uGUQJHaZmMECZmOlix9HnH7n1TRkXMS0pGxIJokIVB9SuqZGGXw==}
    cpu: [arm64]
    os: [linux]
    libc: [musl]

  '@img/sharp-libvips-linuxmusl-x64@1.2.4':
    resolution: {integrity: sha512-+LpyBk7L44ZIXwz/VYfglaX/okxezESc6UxDSoyo2Ks6Jxc4Y7sGjpgU9s4PMgqgjj1gZCylTieNamqA1MF7Dg==}
    cpu: [x64]
    os: [linux]
    libc: [musl]

  '@img/sharp-linux-arm64@0.34.5':
    resolution: {integrity: sha512-bKQzaJRY/bkPOXyKx5EVup7qkaojECG6NLYswgktOZjaXecSAeCWiZwwiFf3/Y+O1HrauiE3FVsGxFg8c24rZg==}
    engines: {node: ^18.17.0 || ^20.3.0 || >=21.0.0}
    cpu: [arm64]
    os: [linux]
    libc: [glibc]

  '@img/sharp-linux-arm@0.34.5':
    resolution: {integrity: sha512-9dLqsvwtg1uuXBGZKsxem9595+ujv0sJ6Vi8wcTANSFpwV/GONat5eCkzQo/1O6zRIkh0m/8+5BjrRr7jDUSZw==}
    engines: {node: ^18.17.0 || ^20.3.0 || >=21.0.0}
    cpu: [arm]
    os: [linux]
    libc: [glibc]

  '@img/sharp-linux-ppc64@0.34.5':
    resolution: {integrity: sha512-7zznwNaqW6YtsfrGGDA6BRkISKAAE1Jo0QdpNYXNMHu2+0dTrPflTLNkpc8l7MUP5M16ZJcUvysVWWrMefZquA==}
    engines: {node: ^18.17.0 || ^20.3.0 || >=21.0.0}
    cpu: [ppc64]
    os: [linux]
    libc: [glibc]

  '@img/sharp-linux-riscv64@0.34.5':
    resolution: {integrity: sha512-51gJuLPTKa7piYPaVs8GmByo7/U7/7TZOq+cnXJIHZKavIRHAP77e3N2HEl3dgiqdD/w0yUfiJnII77PuDDFdw==}
    engines: {node: ^18.17.0 || ^20.3.0 || >=21.0.0}
    cpu: [riscv64]
    os: [linux]
    libc: [glibc]

  '@img/sharp-linux-s390x@0.34.5':
    resolution: {integrity: sha512-nQtCk0PdKfho3eC5MrbQoigJ2gd1CgddUMkabUj+rBevs8tZ2cULOx46E7oyX+04WGfABgIwmMC0VqieTiR4jg==}
    engines: {node: ^18.17.0 || ^20.3.0 || >=21.0.0}
    cpu: [s390x]
    os: [linux]
    libc: [glibc]

  '@img/sharp-linux-x64@0.34.5':
    resolution: {integrity: sha512-MEzd8HPKxVxVenwAa+JRPwEC7QFjoPWuS5NZnBt6B3pu7EG2Ge0id1oLHZpPJdn3OQK+BQDiw9zStiHBTJQQQQ==}
    engines: {node: ^18.17.0 || ^20.3.0 || >=21.0.0}
    cpu: [x64]
    os: [linux]
    libc: [glibc]

  '@img/sharp-linuxmusl-arm64@0.34.5':
    resolution: {integrity: sha512-fprJR6GtRsMt6Kyfq44IsChVZeGN97gTD331weR1ex1c1rypDEABN6Tm2xa1wE6lYb5DdEnk03NZPqA7Id21yg==}
    engines: {node: ^18.17.0 || ^20.3.0 || >=21.0.0}
    cpu: [arm64]
    os: [linux]
    libc: [musl]

  '@img/sharp-linuxmusl-x64@0.34.5':
    resolution: {integrity: sha512-Jg8wNT1MUzIvhBFxViqrEhWDGzqymo3sV7z7ZsaWbZNDLXRJZoRGrjulp60YYtV4wfY8VIKcWidjojlLcWrd8Q==}
    engines: {node: ^18.17.0 || ^20.3.0 || >=21.0.0}
    cpu: [x64]
    os: [linux]
    libc: [musl]

  '@img/sharp-wasm32@0.34.5':
    resolution: {integrity: sha512-OdWTEiVkY2PHwqkbBI8frFxQQFekHaSSkUIJkwzclWZe64O1X4UlUjqqqLaPbUpMOQk6FBu/HtlGXNblIs0huw==}
    engines: {node: ^18.17.0 || ^20.3.0 || >=21.0.0}
    cpu: [wasm32]

  '@img/sharp-win32-arm64@0.34.5':
    resolution: {integrity: sha512-WQ3AgWCWYSb2yt+IG8mnC6Jdk9Whs7O0gxphblsLvdhSpSTtmu69ZG1Gkb6NuvxsNACwiPV6cNSZNzt0KPsw7g==}
    engines: {node: ^18.17.0 || ^20.3.0 || >=21.0.0}
    cpu: [arm64]
    os: [win32]

  '@img/sharp-win32-ia32@0.34.5':
    resolution: {integrity: sha512-FV9m/7NmeCmSHDD5j4+4pNI8Cp3aW+JvLoXcTUo0IqyjSfAZJ8dIUmijx1qaJsIiU+Hosw6xM5KijAWRJCSgNg==}
    engines: {node: ^18.17.0 || ^20.3.0 || >=21.0.0}
    cpu: [ia32]
    os: [win32]

  '@img/sharp-win32-x64@0.34.5':
    resolution: {integrity: sha512-+29YMsqY2/9eFEiW93eqWnuLcWcufowXewwSNIT6UwZdUUCrM3oFjMWH/Z6/TMmb4hlFenmfAVbpWeup2jryCw==}
    engines: {node: ^18.17.0 || ^20.3.0 || >=21.0.0}
    cpu: [x64]
    os: [win32]

  '@internationalized/date@3.12.0':
    resolution: {integrity: sha512-/PyIMzK29jtXaGU23qTvNZxvBXRtKbNnGDFD+PY6CZw/Y8Ex8pFUzkuCJCG9aOqmShjqhS9mPqP6Dk5onQY8rQ==}

  '@internationalized/number@3.6.5':
    resolution: {integrity: sha512-6hY4Kl4HPBvtfS62asS/R22JzNNy8vi/Ssev7x6EobfCp+9QIB2hKvI2EtbdJ0VSQacxVNtqhE/NmF/NZ0gm6g==}

  '@ioredis/commands@1.5.1':
    resolution: {integrity: sha512-JH8ZL/ywcJyR9MmJ5BNqZllXNZQqQbnVZOqpPQqE1vHiFgAw4NHbvE0FOduNU8IX9babitBT46571OnPTT0Zcw==}

  '@isaacs/cliui@8.0.2':
    resolution: {integrity: sha512-O8jcjabXaleOG9DQ0+ARXWZBTfnP4WNAqzuiJK7ll44AmxGKv/J2M4TPjxjY3znBCfvBXFzucm1twdyFybFqEA==}
    engines: {node: '>=12'}

  '@isaacs/fs-minipass@4.0.1':
    resolution: {integrity: sha512-wgm9Ehl2jpeqP3zw/7mo3kRHFp5MEDhqAdwy1fTGkHAwnkGOVsgpvQhL8B5n1qlb01jV3n/bI0ZfZp5lWA1k4w==}
    engines: {node: '>=18.0.0'}

  '@jridgewell/gen-mapping@0.3.13':
    resolution: {integrity: sha512-2kkt/7niJ6MgEPxF0bYdQ6etZaA+fQvDcLKckhy1yIQOzaoKjBBjSj63/aLVjYE3qhRt5dvM+uUyfCg6UKCBbA==}

  '@jridgewell/remapping@2.3.5':
    resolution: {integrity: sha512-LI9u/+laYG4Ds1TDKSJW2YPrIlcVYOwi2fUC6xB43lueCjgxV4lffOCZCtYFiH6TNOX+tQKXx97T4IKHbhyHEQ==}

  '@jridgewell/resolve-uri@3.1.2':
    resolution: {integrity: sha512-bRISgCIjP20/tbWSPWMEi54QVPRZExkuD9lJL+UIxUKtwVJA8wW1Trb1jMs1RFXo1CBTNZ/5hpC9QvmKWdopKw==}
    engines: {node: '>=6.0.0'}

  '@jridgewell/source-map@0.3.11':
    resolution: {integrity: sha512-ZMp1V8ZFcPG5dIWnQLr3NSI1MiCU7UETdS/A0G8V/XWHvJv3ZsFqutJn1Y5RPmAPX6F3BiE397OqveU/9NCuIA==}

  '@jridgewell/sourcemap-codec@1.5.5':
    resolution: {integrity: sha512-cYQ9310grqxueWbl+WuIUIaiUaDcj7WOq5fVhEljNVgRfOUhY9fy2zTvfoqWsnebh8Sl70VScFbICvJnLKB0Og==}

  '@jridgewell/trace-mapping@0.3.31':
    resolution: {integrity: sha512-zzNR+SdQSDJzc8joaeP8QQoCQr8NuYx2dIIytl1QeBEZHJ9uW6hebsrYgbz8hJwUQao3TWCMtmfV8Nu1twOLAw==}

  '@kwsites/file-exists@1.1.1':
    resolution: {integrity: sha512-m9/5YGR18lIwxSFDwfE3oA7bWuq9kdau6ugN4H2rJeyhFQZcG9AgSHkQtSD15a8WvTgfz9aikZMrKPHvbpqFiw==}

  '@kwsites/promise-deferred@1.1.1':
    resolution: {integrity: sha512-GaHYm+c0O9MjZRu0ongGBRbinu8gVAMd2UZjji6jVmqKtZluZnptXGWhz1E8j8D2HJ3f/yMxKAUC0b+57wncIw==}

  '@mapbox/node-pre-gyp@2.0.3':
    resolution: {integrity: sha512-uwPAhccfFJlsfCxMYTwOdVfOz3xqyj8xYL3zJj8f0pb30tLohnnFPhLuqp4/qoEz8sNxe4SESZedcBojRefIzg==}
    engines: {node: '>=18'}
    hasBin: true

  '@modelcontextprotocol/sdk@1.29.0':
    resolution: {integrity: sha512-zo37mZA9hJWpULgkRpowewez1y6ML5GsXJPY8FI0tBBCd77HEvza4jDqRKOXgHNn867PVGCyTdzqpz0izu5ZjQ==}
    engines: {node: '>=18'}
    peerDependencies:
      '@cfworker/json-schema': ^4.1.1
      zod: ^3.25 || ^4.0
    peerDependenciesMeta:
      '@cfworker/json-schema':
        optional: true

  '@napi-rs/wasm-runtime@0.2.12':
    resolution: {integrity: sha512-ZVWUcfwY4E/yPitQJl481FjFo3K22D6qF0DuFH6Y/nbnE11GY5uguDxZMGXPQ8WQ0128MXQD7TnfHyK4oWoIJQ==}

  '@napi-rs/wasm-runtime@1.1.4':
    resolution: {integrity: sha512-3NQNNgA1YSlJb/kMH1ildASP9HW7/7kYnRI2szWJaofaS1hWmbGI4H+d3+22aGzXXN9IJ+n+GiFVcGipJP18ow==}
    peerDependencies:
      '@emnapi/core': ^1.7.1
      '@emnapi/runtime': ^1.7.1

  '@nodelib/fs.scandir@2.1.5':
    resolution: {integrity: sha512-vq24Bq3ym5HEQm2NKCr3yXDwjc7vTsEThRDnkp2DK9p1uqLR+DHurm/NOTo0KG7HYHU7eppKZj3MyqYuMBf62g==}
    engines: {node: '>= 8'}

  '@nodelib/fs.stat@2.0.5':
    resolution: {integrity: sha512-RkhPPp2zrqDAQA/2jNhnztcPAlv64XdhIp7a7454A5ovI7Bukxgt7MX7udwAu3zg1DcpPU0rz3VV1SeaqvY4+A==}
    engines: {node: '>= 8'}

  '@nodelib/fs.walk@1.2.8':
    resolution: {integrity: sha512-oGB+UxlgWcgQkgwo8GcEGwemoTFt3FIO9ababBmaGwXIoBKZ+GTy0pP185beGg7Llih/NSHSV2XAs1lnznocSg==}
    engines: {node: '>= 8'}

  '@nuxt/cli@3.35.1':
    resolution: {integrity: sha512-nX9XO+e3l9pnhHL2zsbnBmQb/nsOQYhGz2XiqE8X962QN9ufc1ZSuDZoTmQVv/ymkbYNR6hpNWW8RZQhuhzadw==}
    engines: {node: ^16.14.0 || >=18.0.0}
    hasBin: true
    peerDependencies:
      '@nuxt/schema': ^4.4.2
    peerDependenciesMeta:
      '@nuxt/schema':
        optional: true

  '@nuxt/content@3.13.0':
    resolution: {integrity: sha512-ZpZ1l0yGzK/Y9QjBT8uReJ62DnOKDMlw+vkzSnkc8YDyZ0ZNhFj1fviMwDhEkArwvQTRfxi12GqzB/wxu01vEw==}
    engines: {node: '>= 20.19.0'}
    peerDependencies:
      '@electric-sql/pglite': '*'
      '@libsql/client': '*'
      '@valibot/to-json-schema': ^1.5.0
      better-sqlite3: ^12.5.0
      sqlite3: '*'
      valibot: ^1.2.0
    peerDependenciesMeta:
      '@electric-sql/pglite':
        optional: true
      '@libsql/client':
        optional: true
      '@valibot/to-json-schema':
        optional: true
      better-sqlite3:
        optional: true
      sqlite3:
        optional: true
      valibot:
        optional: true

  '@nuxt/devalue@2.0.2':
    resolution: {integrity: sha512-GBzP8zOc7CGWyFQS6dv1lQz8VVpz5C2yRszbXufwG/9zhStTIH50EtD87NmWbTMwXDvZLNg8GIpb1UFdH93JCA==}

  '@nuxt/devtools-kit@3.2.4':
    resolution: {integrity: sha512-Yxy2Xgmq5hf3dQy983V0xh0OJV2mYwRZz9eVIGc3EaribdFGPDNGMMbYqX9qCty3Pbxn/bCF3J0UyPaNlHVayQ==}
    peerDependencies:
      vite: '>=6.0'

  '@nuxt/devtools-wizard@3.2.4':
    resolution: {integrity: sha512-5tu2+Quu9XTxwtpzM8CUN0UKn/bzZIfJcoGd+at5Yy1RiUQJ4E52tRK0idW1rMSUDkbkvX3dSnu8Tpj7SAtWdQ==}
    hasBin: true

  '@nuxt/devtools@3.2.4':
    resolution: {integrity: sha512-VPbFy7hlPzWpEZk4BsuVpNuHq1ZYGV9xezjb7/NGuePuNLqeNn74YZugU+PCtva7OwKhEeTXmMK0Mqo/6+nwNA==}
    hasBin: true
    peerDependencies:
      '@vitejs/devtools': '*'
      vite: '>=6.0'
    peerDependenciesMeta:
      '@vitejs/devtools':
        optional: true

  '@nuxt/eslint-config@1.15.2':
    resolution: {integrity: sha512-vS6mWB87tYjB8h3TxG/QziaZ6CGJpEOBd7N/j+64/tjNipUJzNgKwDzyGoOifNqyDDnlvgi6T3m9XpeYm4qRaA==}
    peerDependencies:
      eslint: ^9.0.0 || ^10.0.0
      eslint-plugin-format: '*'
    peerDependenciesMeta:
      eslint-plugin-format:
        optional: true

  '@nuxt/eslint-plugin@1.15.2':
    resolution: {integrity: sha512-LZ4gEcPP5GjzAkb6Kk04a4v0vvkTLOpmnEvdDatnkSlxtQLUSwX8v11vcDGXL92ZQ98dFoC1Q1IA6Tz3jdFIig==}
    peerDependencies:
      eslint: ^9.0.0 || ^10.0.0

  '@nuxt/eslint@1.15.2':
    resolution: {integrity: sha512-LwDavQoLl+y0sIDqWEYbOnM6FOmXVIYSEjuvkO1hgAqhb0CvG3hgTnfE1qkf1jOAZp3CZGP+6rxRAJ0dxhueIQ==}
    peerDependencies:
      eslint: ^9.0.0 || ^10.0.0
      eslint-webpack-plugin: ^4.1.0
      vite-plugin-eslint2: ^5.0.0
    peerDependenciesMeta:
      eslint-webpack-plugin:
        optional: true
      vite-plugin-eslint2:
        optional: true

  '@nuxt/fonts@0.14.0':
    resolution: {integrity: sha512-4uXQl9fa5F4ibdgU8zomoOcyMdnwgdem+Pi8JEqeDYI5yPR32Kam6HnuRr47dTb97CstaepAvXPWQUUHMtjsFQ==}

  '@nuxt/icon@2.2.1':
    resolution: {integrity: sha512-GI840yYGuvHI0BGDQ63d6rAxGzG96jQcWrnaWIQKlyQo/7sx9PjXkSHckXUXyX1MCr9zY6U25Td6OatfY6Hklw==}

  '@nuxt/image@2.0.0':
    resolution: {integrity: sha512-otHi6gAoYXKLrp8m27ZjX1PjxOPaltQ4OiUs/BhkW995mF/vXf8SWQTw68fww+Uric0v+XgoVrP9icDi+yT6zw==}
    engines: {node: '>=18.20.6'}

  '@nuxt/kit@3.21.2':
    resolution: {integrity: sha512-Bd6m6mrDrqpBEbX+g0rc66/ALd1sxlgdx5nfK9MAYO0yKLTOSK7McSYz1KcOYn3LQFCXOWfvXwaqih/b+REI1g==}
    engines: {node: '>=18.12.0'}

  '@nuxt/kit@4.4.5':
    resolution: {integrity: sha512-J0BpoOomzd3iVZozYlZJ7AwAVliXRgeChZnAkQLfg8d0h/Q+aMK9kkHuhwFULASaRn5idiD4BIhOUz7/uoLbSw==}
    engines: {node: '>=18.12.0'}

  '@nuxt/nitro-server@4.4.5':
    resolution: {integrity: sha512-ZxmfxZbQ6Yr/DYkuGmPFtE/A1hDbbcOurlPeh/H4oHfAkv/N6W7OWg/3PGViKwckmF69jUMe/a89HAguaH+r5A==}
    engines: {node: ^20.19.0 || >=22.12.0}
    peerDependencies:
      '@babel/plugin-proposal-decorators': ^7.25.0
      '@rollup/plugin-babel': ^6.0.0 || ^7.0.0
      nuxt: ^4.4.5
    peerDependenciesMeta:
      '@babel/plugin-proposal-decorators':
        optional: true
      '@rollup/plugin-babel':
        optional: true

  '@nuxt/schema@4.4.5':
    resolution: {integrity: sha512-kPacVsBInUgM3JiFiHUGd5fr8Ohe+79PGrBwjipfGzA61UMPfj7CmPuKrvmL1i4oLS1I3/flHvU5VFVyQ/wyxQ==}
    engines: {node: ^14.18.0 || >=16.10.0}

  '@nuxt/telemetry@2.8.0':
    resolution: {integrity: sha512-zAwXY24KYvpLTmiV+osagd2EHkfs5IF+7oDZYTQoit5r0kPlwaCNlzHp5I/wUAWT4LBw6lG8gZ6bWidAdv/erQ==}
    engines: {node: '>=18.12.0'}
    hasBin: true
    peerDependencies:
      '@nuxt/kit': '>=3.0.0'

  '@nuxt/ui@4.7.1':
    resolution: {integrity: sha512-s3Ix89RkJTeNDlLg7EflckkFxQgzm2W9bt4CBsudi7wNdmhbb3nzYG6rcns2R2Wos0gZlYkSfDKaX1o3zMC+Aw==}
    engines: {node: ^20.19.0 || >=22.12.0}
    hasBin: true
    peerDependencies:
      '@inertiajs/vue3': ^2.0.7 || ^3.0.0
      '@internationalized/date': ^3.0.0
      '@internationalized/number': ^3.0.0
      '@nuxt/content': ^3.0.0
      joi: ^18.0.0
      superstruct: ^2.0.0
      tailwindcss: ^4.0.0
      typescript: ^5.6.3 || ^6.0.0
      valibot: ^1.0.0
      vue-router: ^4.5.0 || ^5.0.0
      yup: ^1.7.0
      zod: ^3.24.0 || ^4.0.0
    peerDependenciesMeta:
      '@inertiajs/vue3':
        optional: true
      '@internationalized/date':
        optional: true
      '@internationalized/number':
        optional: true
      '@nuxt/content':
        optional: true
      joi:
        optional: true
      superstruct:
        optional: true
      valibot:
        optional: true
      vue-router:
        optional: true
      yup:
        optional: true
      zod:
        optional: true

  '@nuxt/vite-builder@4.4.5':
    resolution: {integrity: sha512-PLb1a3yjSES6CEAKqCuT9qPqT7xLtf5VH3XeE3rZ0iBQ+ReVkglwouE+M/lRR61R7PjlvAszjOyjnKbOG1pOAg==}
    engines: {node: ^20.19.0 || >=22.12.0}
    peerDependencies:
      '@babel/plugin-proposal-decorators': ^7.25.0
      '@babel/plugin-syntax-jsx': ^7.25.0
      nuxt: 4.4.5
      rolldown: ^1.0.0-beta.38
      rollup-plugin-visualizer: ^6.0.0 || ^7.0.1
      vue: ^3.3.4
    peerDependenciesMeta:
      '@babel/plugin-proposal-decorators':
        optional: true
      '@babel/plugin-syntax-jsx':
        optional: true
      rolldown:
        optional: true
      rollup-plugin-visualizer:
        optional: true

  '@nuxtjs/color-mode@3.5.2':
    resolution: {integrity: sha512-cC6RfgZh3guHBMLLjrBB2Uti5eUoGM9KyauOaYS9ETmxNWBMTvpgjvSiSJp1OFljIXPIqVTJ3xtJpSNZiO3ZaA==}

  '@nuxtjs/mcp-toolkit@0.16.1':
    resolution: {integrity: sha512-dHGaBLs9dFI9m9l8CZcg9JtkBkV9sw/wRC6iqTZ9HcRWO5RciZxnH9XlBIAxXTgHLdMRQTv48ZgImT2bP41U8g==}
    peerDependencies:
      '@vue/compiler-sfc': ^3.5.33
      agents: '>=0.12.3'
      h3: '>=1.15.11'
      secure-exec: '>=0.2.1'
      vite: ^5.0.0 || ^6.0.0 || ^7.0.0 || ^8.0.0
      vue: ^3.5.33
      zod: ^4.1.13
    peerDependenciesMeta:
      '@vue/compiler-sfc':
        optional: true
      agents:
        optional: true
      secure-exec:
        optional: true
      vite:
        optional: true
      vue:
        optional: true

  '@nuxtjs/mdc@0.21.1':
    resolution: {integrity: sha512-DIeUD7IahWVUSoZExysxH9dX51Io6hcQYgGJODq0cMTGqaoDD32lRfHBJxYUmy+sUCV1+1hfa2ixspgJgEd2GA==}

  '@oxc-minify/binding-android-arm-eabi@0.128.0':
    resolution: {integrity: sha512-EwdDhZLRmXxSnfy0v9gdOru7TutM8ItRg1Xv8e2B4boWMnHlFCIH38JfwgQnenbkF8SVTwVJtDCkmwEzN4q3xA==}
    engines: {node: ^20.19.0 || >=22.12.0}
    cpu: [arm]
    os: [android]

  '@oxc-minify/binding-android-arm64@0.128.0':
    resolution: {integrity: sha512-kwJ8YxWTzty8hD36jXxKiB+Po/ecmHZvT1xAYklkATbr0A4NUqV32sV+3Wfm8TecdA6jX34/mc+4CKK2+Hha2Q==}
    engines: {node: ^20.19.0 || >=22.12.0}
    cpu: [arm64]
    os: [android]

  '@oxc-minify/binding-darwin-arm64@0.128.0':
    resolution: {integrity: sha512-WBV8j5EZ7/3rvFbiJ8LxowmobR/XH+l2iRzkE7zRYLD5VC+TvZayYGrVGGDXQvXm6cGED0B1NweByTmeT4lpGQ==}
    engines: {node: ^20.19.0 || >=22.12.0}
    cpu: [arm64]
    os: [darwin]

  '@oxc-minify/binding-darwin-x64@0.128.0':
    resolution: {integrity: sha512-U4k1CSBsY1uf6yHE+vCNJp0mHzjsUUXgOZXMyhRN3sE2ovBDT9Gl8oACmLWPjg0R68jwP+1vhnNPsSqpTEOycg==}
    engines: {node: ^20.19.0 || >=22.12.0}
    cpu: [x64]
    os: [darwin]

  '@oxc-minify/binding-freebsd-x64@0.128.0':
    resolution: {integrity: sha512-NT1GtcWpX4sOuU5dMdSNpdXJRpk9BGAHHnKc42IUId8E+jEhZUrg9vqIRIlspZG5O9Y7FjO2r6GBK93bpyIIUg==}
    engines: {node: ^20.19.0 || >=22.12.0}
    cpu: [x64]
    os: [freebsd]

  '@oxc-minify/binding-linux-arm-gnueabihf@0.128.0':
    resolution: {integrity: sha512-OskPMYMH2KtkqvRMULF2/+55hFo/qmRz2p/g7Cp7XNiqdjZ/DvQDiVbME63rVoX3dYjgS15DolGbo54mHTyA9w==}
    engines: {node: ^20.19.0 || >=22.12.0}
    cpu: [arm]
    os: [linux]

  '@oxc-minify/binding-linux-arm-musleabihf@0.128.0':
    resolution: {integrity: sha512-fKUY7Y1vb8CYlGnS5FzqTeeM5zQz1Fleyaqz/T9iNHYAYNJ0Os9iT0rACLfAVCQKP9yOqPSwZ80xgZdVVGD61w==}
    engines: {node: ^20.19.0 || >=22.12.0}
    cpu: [arm]
    os: [linux]

  '@oxc-minify/binding-linux-arm64-gnu@0.128.0':
    resolution: {integrity: sha512-T+CQQZ3BoWY/TxQk9LZsXZYj3madR/5tCErV6wzphTYZJfVjvKmQxnxMaT+TKE40Jha6+iGgwzxwcYWJfltULQ==}
    engines: {node: ^20.19.0 || >=22.12.0}
    cpu: [arm64]
    os: [linux]
    libc: [glibc]

  '@oxc-minify/binding-linux-arm64-musl@0.128.0':
    resolution: {integrity: sha512-F6RkJ90S1Xt25Mk7/wPUmddsE4RZ7Nei+HlEa2FAjfhpoaTciOwV6E/Gtp7wPIYbwft7UfhMYwuEuZiZQytVWw==}
    engines: {node: ^20.19.0 || >=22.12.0}
    cpu: [arm64]
    os: [linux]
    libc: [musl]

  '@oxc-minify/binding-linux-ppc64-gnu@0.128.0':
    resolution: {integrity: sha512-0HP2FBGMlquLjShIIJvS4cebc6sdRRYL04GtxVpg96MtpejrkHYI2gQWcezsTUaGgg+eNRsuv2tdZPENu5+iWA==}
    engines: {node: ^20.19.0 || >=22.12.0}
    cpu: [ppc64]
    os: [linux]
    libc: [glibc]

  '@oxc-minify/binding-linux-riscv64-gnu@0.128.0':
    resolution: {integrity: sha512-2j6Bd340IZqZbu4KUI28z87Ao9aHhq56HH1Qz5/+EdE732ajFYIoDF3z+QcxHXY0CFOG/Ur1ZOKTBEIWQ6BYIw==}
    engines: {node: ^20.19.0 || >=22.12.0}
    cpu: [riscv64]
    os: [linux]
    libc: [glibc]

  '@oxc-minify/binding-linux-riscv64-musl@0.128.0':
    resolution: {integrity: sha512-z5HSppdxNwB6//3Eo7mDWbTrLeyuTKvL/iLXaKEgocrJg1MhZLbRR7P5ore9gKvS4lF4EtEpA24xzilFxQK0iw==}
    engines: {node: ^20.19.0 || >=22.12.0}
    cpu: [riscv64]
    os: [linux]
    libc: [musl]

  '@oxc-minify/binding-linux-s390x-gnu@0.128.0':
    resolution: {integrity: sha512-9rxYqH7P8NiYqRlLxlnNjJSF8BYADOmihM5ZHVkmlE4tqjHkoLNevdAyAP2ZBkL8QJflm1WGOXFWmFnWA54EvA==}
    engines: {node: ^20.19.0 || >=22.12.0}
    cpu: [s390x]
    os: [linux]
    libc: [glibc]

  '@oxc-minify/binding-linux-x64-gnu@0.128.0':
    resolution: {integrity: sha512-sy5+4Oamw6Ly5gUNUIDQ7346Lryt7AhqjKhOtWl5dzYZnTIwwoI0V2DeIl3bR/vU8D629ZMYQOqhquRtSyBUOA==}
    engines: {node: ^20.19.0 || >=22.12.0}
    cpu: [x64]
    os: [linux]
    libc: [glibc]

  '@oxc-minify/binding-linux-x64-musl@0.128.0':
    resolution: {integrity: sha512-59Cxvjppy09TsaB15gr6rA9Bf87rm9t0bD1EW9dCZsdxWElnAC+TvWZ7v9dFUIeYeZUkhAAMPtpdqa3Y9CI2zA==}
    engines: {node: ^20.19.0 || >=22.12.0}
    cpu: [x64]
    os: [linux]
    libc: [musl]

  '@oxc-minify/binding-openharmony-arm64@0.128.0':
    resolution: {integrity: sha512-XGa03zmiYpD7Kf1aXy6vjgkjfaCR90qH0TzGplnUXo6FF6gNe6sH9Zgneo9kxOyYt8CKKzXYD4VudT/nDTXq8Q==}
    engines: {node: ^20.19.0 || >=22.12.0}
    cpu: [arm64]
    os: [openharmony]

  '@oxc-minify/binding-wasm32-wasi@0.128.0':
    resolution: {integrity: sha512-W+fK3cWhu/cUgx3NIAmDYcAyJs01aULlr3E3n/ZN79Q1/CX+FS+yWfwt/IysIi4FhpVL7z58azbJHDzhEx4X4g==}
    engines: {node: ^20.19.0 || >=22.12.0}
    cpu: [wasm32]

  '@oxc-minify/binding-win32-arm64-msvc@0.128.0':
    resolution: {integrity: sha512-pwMZd27FF+j4tHLYKtu4QBl6KI0gkt6xTNGLffs8VlH5vfDPHUvLo/AS6y66tdEjQ3chhs8OGg1mAFhPoQldDw==}
    engines: {node: ^20.19.0 || >=22.12.0}
    cpu: [arm64]
    os: [win32]

  '@oxc-minify/binding-win32-ia32-msvc@0.128.0':
    resolution: {integrity: sha512-GskPdx/Fsn3ttkJbzxh51LYhla4N4p1sMufJKgf6PHupt5RukBaHI/GKM/2ni6ObxUI0b9UK37fROdV+5ekpMQ==}
    engines: {node: ^20.19.0 || >=22.12.0}
    cpu: [ia32]
    os: [win32]

  '@oxc-minify/binding-win32-x64-msvc@0.128.0':
    resolution: {integrity: sha512-m8oakspZCbCod3WuY0U9DvwQlhMYaU31bK+Way1Rb+JGs455WLtkebEie/luSuN5DeF+aZyRH/zt1AY4weKQQg==}
    engines: {node: ^20.19.0 || >=22.12.0}
    cpu: [x64]
    os: [win32]

  '@oxc-parser/binding-android-arm-eabi@0.128.0':
    resolution: {integrity: sha512-aca6ZvzmCBUGOANQRiRQRZuRKYI3ENhcit6GisnknOOmcezfQc7xJ4dxlPU7MV7mOvrC7RNR1u3LAD7xyaiCxA==}
    engines: {node: ^20.19.0 || >=22.12.0}
    cpu: [arm]
    os: [android]

  '@oxc-parser/binding-android-arm64@0.128.0':
    resolution: {integrity: sha512-BbeDmuohoJ7Rz/it5wnkj69i/OsCPS3Z51nLEzwO/Y6YshtC4JU+15oNwhY8v4LRKRYclRc7ggOikwrsJ/eOEQ==}
    engines: {node: ^20.19.0 || >=22.12.0}
    cpu: [arm64]
    os: [android]

  '@oxc-parser/binding-darwin-arm64@0.128.0':
    resolution: {integrity: sha512-tRUHPt80417QmvNpoSslJT1VY8NUbWdrWR+L14Zn+RbOTcaqB8E6PYE/ZGN8jjWBzqporiA/H4MfO50ew/NCNA==}
    engines: {node: ^20.19.0 || >=22.12.0}
    cpu: [arm64]
    os: [darwin]

  '@oxc-parser/binding-darwin-x64@0.128.0':
    resolution: {integrity: sha512-rWI2Hb1Nt3U/vKsjyNvZzDC8i/l144U20DKjhzaTmwIhIiSRGeroPWWiImwypmKLqrw8GuIixbWJkpGWLbkzrQ==}
    engines: {node: ^20.19.0 || >=22.12.0}
    cpu: [x64]
    os: [darwin]

  '@oxc-parser/binding-freebsd-x64@0.128.0':
    resolution: {integrity: sha512-hhpdVMaNCLgQxjgNPeeFzSeJMmZPc5lKfv0NGSI3egZq9EdnEGqeC8JsYsQjK7PoQgbvZ17xlj0SO5ziH5Obkg==}
    engines: {node: ^20.19.0 || >=22.12.0}
    cpu: [x64]
    os: [freebsd]

  '@oxc-parser/binding-linux-arm-gnueabihf@0.128.0':
    resolution: {integrity: sha512-093zNw0zZ/e/obML+rhlSdmnzR0mVZluPcAkxunEc5E3F0yBVsFn24Y1ILfsEte11Ud041qn/gp2OJ1jxNqUng==}
    engines: {node: ^20.19.0 || >=22.12.0}
    cpu: [arm]
    os: [linux]

  '@oxc-parser/binding-linux-arm-musleabihf@0.128.0':
    resolution: {integrity: sha512-fq7DmKmfC+dvD97IXrgbph6Jzwe0EDu+PYMofmzZ6fv5X1k9vtaqLpDGMuICO9MmUnyKAQmVl+wIv2RNy4Dz8g==}
    engines: {node: ^20.19.0 || >=22.12.0}
    cpu: [arm]
    os: [linux]

  '@oxc-parser/binding-linux-arm64-gnu@0.128.0':
    resolution: {integrity: sha512-Xvm48jJah8TlIrURIjNOP/gNiGe6aKvCB+r06VliflFo8Kq7VOLE8PxtgShJzZIqubrgdMdYfvuPPozn7F6MbQ==}
    engines: {node: ^20.19.0 || >=22.12.0}
    cpu: [arm64]
    os: [linux]
    libc: [glibc]

  '@oxc-parser/binding-linux-arm64-musl@0.128.0':
    resolution: {integrity: sha512-M7iwBGmYJTx+pKOYFjI0buop4gJvlmcVzFGaXPt21DKpQkbQZG1f63Yg7LloIYT/t9yLxCw0Lhfx/RFlAlMSjA==}
    engines: {node: ^20.19.0 || >=22.12.0}
    cpu: [arm64]
    os: [linux]
    libc: [musl]

  '@oxc-parser/binding-linux-ppc64-gnu@0.128.0':
    resolution: {integrity: sha512-21LGNIZb1Pcfk5/EGsqabrxv4yqQOWis1407JJrClS7XpFCrbvr74YAB1V+m54cYbwvO6UWwQqS4WecxiyfCRg==}
    engines: {node: ^20.19.0 || >=22.12.0}
    cpu: [ppc64]
    os: [linux]
    libc: [glibc]

  '@oxc-parser/binding-linux-riscv64-gnu@0.128.0':
    resolution: {integrity: sha512-gyHjOTFpg9bTTYjxPmQirvufb89+VdZwVfcMtAUyPr6F5H8ZswvCQshK4qOW+Q+2Xyb33hduRgY/eFHJQjU/vQ==}
    engines: {node: ^20.19.0 || >=22.12.0}
    cpu: [riscv64]
    os: [linux]
    libc: [glibc]

  '@oxc-parser/binding-linux-riscv64-musl@0.128.0':
    resolution: {integrity: sha512-X6Q2oKUrP5GyDd2xniuEBLk6aFQCZ97W2+aVXGgJXdjx5t4/oFuA9ri0wLOUrBIX+qdSuK581snMBio4z910eA==}
    engines: {node: ^20.19.0 || >=22.12.0}
    cpu: [riscv64]
    os: [linux]
    libc: [musl]

  '@oxc-parser/binding-linux-s390x-gnu@0.128.0':
    resolution: {integrity: sha512-BdzTmqxfxoYkpgokoLaSnOX6T+R3/goL42klre2tnG+kHbG2TXS0VN+P5BPofH1axdKOHy5ei4ENZrjmCOt2lA==}
    engines: {node: ^20.19.0 || >=22.12.0}
    cpu: [s390x]
    os: [linux]
    libc: [glibc]

  '@oxc-parser/binding-linux-x64-gnu@0.128.0':
    resolution: {integrity: sha512-OO1nW2Q7sSYYvJZpDHdvyFSdRaVcQqRijZSSmWVMqFxPYy8cEF45zJ9fcdIYuzIT3jYq6YRhEFm/VMWNWhE22Q==}
    engines: {node: ^20.19.0 || >=22.12.0}
    cpu: [x64]
    os: [linux]
    libc: [glibc]

  '@oxc-parser/binding-linux-x64-musl@0.128.0':
    resolution: {integrity: sha512-4NehAe404MRdoZVS9DW8C5XbJwbXIc/KfVlYdpi5vE4081zc9Y0YzKVqyOYj/Puye7/Do+ohaONBFWlEHYl9hw==}
    engines: {node: ^20.19.0 || >=22.12.0}
    cpu: [x64]
    os: [linux]
    libc: [musl]

  '@oxc-parser/binding-openharmony-arm64@0.128.0':
    resolution: {integrity: sha512-kVbqgW9xLL8bh8oc7aYOJilRKXE5G33+tE0jan+duo/9OriaFRpijcCwT2waWs2oqYROYq0GlE7/p3ywoshVeg==}
    engines: {node: ^20.19.0 || >=22.12.0}
    cpu: [arm64]
    os: [openharmony]

  '@oxc-parser/binding-wasm32-wasi@0.128.0':
    resolution: {integrity: sha512-L38ojghJYHmgiz6fJd7jwLB/ESDBpB02NdFxh+smqVM6P2anCEvHn0jhaSrt5eVNR1Ak8+moOeftUlofeyvniA==}
    engines: {node: ^20.19.0 || >=22.12.0}
    cpu: [wasm32]

  '@oxc-parser/binding-win32-arm64-msvc@0.128.0':
    resolution: {integrity: sha512-xgvO35GyHBtjlQ5AEpaYr7Rll1rvY7zqIhT6ty8E3ezBW2J1SFLjIDEvI/tcgDg6oaseDAqVcM+jU1HuCekgZw==}
    engines: {node: ^20.19.0 || >=22.12.0}
    cpu: [arm64]
    os: [win32]

  '@oxc-parser/binding-win32-ia32-msvc@0.128.0':
    resolution: {integrity: sha512-OY+3eM2SN72prHKRB22mPz8o5A/7dJ+f5DFLBVvggyZhEaNDAH9IB+ElMjmOkOIwf5MDCUAowCK7pAncNxzpBA==}
    engines: {node: ^20.19.0 || >=22.12.0}
    cpu: [ia32]
    os: [win32]

  '@oxc-parser/binding-win32-x64-msvc@0.128.0':
    resolution: {integrity: sha512-NE9ny+cPUCCObXa0IKLfj0tCdPd7pe/dz9ZpkxpUOymB3miNeMPybdlYYTBSGJUalMWeBM85/4JcCErCNTqOXw==}
    engines: {node: ^20.19.0 || >=22.12.0}
    cpu: [x64]
    os: [win32]

  '@oxc-project/types@0.128.0':
    resolution: {integrity: sha512-huv1Y/LzBJkBVHt3OlC7u0zHBW9qXf1FdD7sGmc1rXc2P1mTwHssYv7jyGx5KAACSCH+9B3Bhn6Z9luHRvf7pQ==}

  '@oxc-transform/binding-android-arm-eabi@0.128.0':
    resolution: {integrity: sha512-qVO4izEs88ZSo7KOK4P+O5nAXXJmkSadInvFjGkhVnm2R2Wr8trU/GLhjAK0S0u8Qv9bkXspNhgpECk+CTQ/ew==}
    engines: {node: ^20.19.0 || >=22.12.0}
    cpu: [arm]
    os: [android]

  '@oxc-transform/binding-android-arm64@0.128.0':
    resolution: {integrity: sha512-F3RXlbCzIgkpRWlz1PEguDZl5NzZRmbeHKTFTQWFnK6mIdw2EkWihPVv9+CIcO80c7+sF/YRGOBaji6hwUDhtQ==}
    engines: {node: ^20.19.0 || >=22.12.0}
    cpu: [arm64]
    os: [android]

  '@oxc-transform/binding-darwin-arm64@0.128.0':
    resolution: {integrity: sha512-xj63gIzQ67LDYHCOWXSHgfx4LbPVz1ck0G3y0eR6mbgYk3CwwylbhWi/CaDC6BWsHwoLQryeYjHB5XBCR0EPMQ==}
    engines: {node: ^20.19.0 || >=22.12.0}
    cpu: [arm64]
    os: [darwin]

  '@oxc-transform/binding-darwin-x64@0.128.0':
    resolution: {integrity: sha512-YQkvFqNqpwEt197RjREAOWeRANalPtCD+ayZlx4IjTQ6IOYZEP83B9/++gTQisHV3r8E7dU8UqJKeSS1cHlTQg==}
    engines: {node: ^20.19.0 || >=22.12.0}
    cpu: [x64]
    os: [darwin]

  '@oxc-transform/binding-freebsd-x64@0.128.0':
    resolution: {integrity: sha512-Jvd3Ximb3x3o0+xRBB5lq63JlzxhJN787IsBjn0PEnmuocYQj+tJ5BB4n9xPIG27GXwg3ycckQPO/RsWeEcBPg==}
    engines: {node: ^20.19.0 || >=22.12.0}
    cpu: [x64]
    os: [freebsd]

  '@oxc-transform/binding-linux-arm-gnueabihf@0.128.0':
    resolution: {integrity: sha512-TaRKWeGnAJNIdCa5+m0I8/SksBgkLX94iH40qy3chvLuaIOGAmOViUStYx8geXBzO9P99V7En8nHXLoqCONBRQ==}
    engines: {node: ^20.19.0 || >=22.12.0}
    cpu: [arm]
    os: [linux]

  '@oxc-transform/binding-linux-arm-musleabihf@0.128.0':
    resolution: {integrity: sha512-7TMrtA5/3SCvS+yMPrGnri5T4ZhIoCbjwKWV6Kn8d3v+vx7MpEmNkfe+CdF3rb5LlnuxeDMPwr1E2ntya0b8HQ==}
    engines: {node: ^20.19.0 || >=22.12.0}
    cpu: [arm]
    os: [linux]

  '@oxc-transform/binding-linux-arm64-gnu@0.128.0':
    resolution: {integrity: sha512-lMQEa1jLBNm1N+5uvyj9zX9urVY4xKkLnhO8/4CtSGdXX+mExqsVawyQPAZqbtq1fLQ0yt1QYJ9YuM0+fiSJTQ==}
    engines: {node: ^20.19.0 || >=22.12.0}
    cpu: [arm64]
    os: [linux]
    libc: [glibc]

  '@oxc-transform/binding-linux-arm64-musl@0.128.0':
    resolution: {integrity: sha512-dPSjyd0gQ9dE3mpdJi0BHNJaqQz4V7mVW6Fbs6jRSiGnrxwGfXdMJFInXoJ49B3k5Zhfa9Is9Ixp6St7c6ouCA==}
    engines: {node: ^20.19.0 || >=22.12.0}
    cpu: [arm64]
    os: [linux]
    libc: [musl]

  '@oxc-transform/binding-linux-ppc64-gnu@0.128.0':
    resolution: {integrity: sha512-YNa9XAotPKvAXFJrHC7kBsHMVg0HOB4vRiKuYUjzFsfLkxTbuztKHTKG/gW5kjp7dBw+TNFofTaVCVZgOnHXPQ==}
    engines: {node: ^20.19.0 || >=22.12.0}
    cpu: [ppc64]
    os: [linux]
    libc: [glibc]

  '@oxc-transform/binding-linux-riscv64-gnu@0.128.0':
    resolution: {integrity: sha512-jjSiG9H8ya/U3igW5DdIBFIDwhffF7Vbc7th2tcHV73eg0DQz75n36a9RmQ1/0aS9vknUuNtY6SODr8/gmuzsQ==}
    engines: {node: ^20.19.0 || >=22.12.0}
    cpu: [riscv64]
    os: [linux]
    libc: [glibc]

  '@oxc-transform/binding-linux-riscv64-musl@0.128.0':
    resolution: {integrity: sha512-FVUr/XNT7BfQA4XVMel/HTCJi5mQyEitslgX42ztYPnCFMRFG1sQQKgnlLJdl7qifuyxpvKLR1f7h7HEuwWw1Q==}
    engines: {node: ^20.19.0 || >=22.12.0}
    cpu: [riscv64]
    os: [linux]
    libc: [musl]

  '@oxc-transform/binding-linux-s390x-gnu@0.128.0':
    resolution: {integrity: sha512-caJnVw5PG8v339zAyHgA7p34xXa3A4Kc9VyrDgsT1znr51qacaUv4BRlgRi0qkqxRWXYNVFfsbU2g0t1qS7E9w==}
    engines: {node: ^20.19.0 || >=22.12.0}
    cpu: [s390x]
    os: [linux]
    libc: [glibc]

  '@oxc-transform/binding-linux-x64-gnu@0.128.0':
    resolution: {integrity: sha512-zkQKjsHEUX3ckQBcZTtHE/7pgFMkWQp6y/4t7N8eT3j8wnoL+vapv7l4ISjgx1/EePRJN1HErYXmriz7tPVKRg==}
    engines: {node: ^20.19.0 || >=22.12.0}
    cpu: [x64]
    os: [linux]
    libc: [glibc]

  '@oxc-transform/binding-linux-x64-musl@0.128.0':
    resolution: {integrity: sha512-NjYtwl9ijp34iisHxYBvE7nii1Ac0QPP3doHv8MQHhDA3zjUcDCROuBNybfaEYCxnJ1aF+cAPqsyeopnAGsyuQ==}
    engines: {node: ^20.19.0 || >=22.12.0}
    cpu: [x64]
    os: [linux]
    libc: [musl]

  '@oxc-transform/binding-openharmony-arm64@0.128.0':
    resolution: {integrity: sha512-itsi0tVkVdrYphSppdFChLq9tD0pvbRRS3EV8NQYKZ/NWHMoxzjlf9TFA/ZZYV113juYo1Dq3glVX48knhBeFQ==}
    engines: {node: ^20.19.0 || >=22.12.0}
    cpu: [arm64]
    os: [openharmony]

  '@oxc-transform/binding-wasm32-wasi@0.128.0':
    resolution: {integrity: sha512-elzjX2gy1jcseeFaKtbk/6T2FPTpGNx0IpeD0iyk6cahWN7wD6eHY5u7th1X85cYbRq9rqniS+xYIxN3StthWg==}
    engines: {node: ^20.19.0 || >=22.12.0}
    cpu: [wasm32]

  '@oxc-transform/binding-win32-arm64-msvc@0.128.0':
    resolution: {integrity: sha512-p5LmbI66dk2dziJSUzjQ24gOWeI6pJpXcOC6famloRtKCq54V5/KegsztFgZZCtYFEAEqFgcfspFHrV+CcKWcg==}
    engines: {node: ^20.19.0 || >=22.12.0}
    cpu: [arm64]
    os: [win32]

  '@oxc-transform/binding-win32-ia32-msvc@0.128.0':
    resolution: {integrity: sha512-CMU3Yn05rXeLw7GyVlDB3bbp2iV14yt3VWyF0pNuMK9NVgOmUkXgFLe5SOcX9rEm64TRJjOMEghtE5+r0GtqIQ==}
    engines: {node: ^20.19.0 || >=22.12.0}
    cpu: [ia32]
    os: [win32]

  '@oxc-transform/binding-win32-x64-msvc@0.128.0':
    resolution: {integrity: sha512-Vck5AdNH2JPYMQWVDxvX5PbDFfqVG+tCOgKJzAC/S9bgbD3qcMjN5Dx6FOmEbwY3hZm//fzOsY4tErofoiK/aQ==}
    engines: {node: ^20.19.0 || >=22.12.0}
    cpu: [x64]
    os: [win32]

  '@package-json/types@0.0.12':
    resolution: {integrity: sha512-uu43FGU34B5VM9mCNjXCwLaGHYjXdNincqKLaraaCW+7S2+SmiBg1Nv8bPnmschrIfZmfKNY9f3fC376MRrObw==}

  '@parcel/watcher-android-arm64@2.5.6':
    resolution: {integrity: sha512-YQxSS34tPF/6ZG7r/Ih9xy+kP/WwediEUsqmtf0cuCV5TPPKw/PQHRhueUo6JdeFJaqV3pyjm0GdYjZotbRt/A==}
    engines: {node: '>= 10.0.0'}
    cpu: [arm64]
    os: [android]

  '@parcel/watcher-darwin-arm64@2.5.6':
    resolution: {integrity: sha512-Z2ZdrnwyXvvvdtRHLmM4knydIdU9adO3D4n/0cVipF3rRiwP+3/sfzpAwA/qKFL6i1ModaabkU7IbpeMBgiVEA==}
    engines: {node: '>= 10.0.0'}
    cpu: [arm64]
    os: [darwin]

  '@parcel/watcher-darwin-x64@2.5.6':
    resolution: {integrity: sha512-HgvOf3W9dhithcwOWX9uDZyn1lW9R+7tPZ4sug+NGrGIo4Rk1hAXLEbcH1TQSqxts0NYXXlOWqVpvS1SFS4fRg==}
    engines: {node: '>= 10.0.0'}
    cpu: [x64]
    os: [darwin]

  '@parcel/watcher-freebsd-x64@2.5.6':
    resolution: {integrity: sha512-vJVi8yd/qzJxEKHkeemh7w3YAn6RJCtYlE4HPMoVnCpIXEzSrxErBW5SJBgKLbXU3WdIpkjBTeUNtyBVn8TRng==}
    engines: {node: '>= 10.0.0'}
    cpu: [x64]
    os: [freebsd]

  '@parcel/watcher-linux-arm-glibc@2.5.6':
    resolution: {integrity: sha512-9JiYfB6h6BgV50CCfasfLf/uvOcJskMSwcdH1PHH9rvS1IrNy8zad6IUVPVUfmXr+u+Km9IxcfMLzgdOudz9EQ==}
    engines: {node: '>= 10.0.0'}
    cpu: [arm]
    os: [linux]
    libc: [glibc]

  '@parcel/watcher-linux-arm-musl@2.5.6':
    resolution: {integrity: sha512-Ve3gUCG57nuUUSyjBq/MAM0CzArtuIOxsBdQ+ftz6ho8n7s1i9E1Nmk/xmP323r2YL0SONs1EuwqBp2u1k5fxg==}
    engines: {node: '>= 10.0.0'}
    cpu: [arm]
    os: [linux]
    libc: [musl]

  '@parcel/watcher-linux-arm64-glibc@2.5.6':
    resolution: {integrity: sha512-f2g/DT3NhGPdBmMWYoxixqYr3v/UXcmLOYy16Bx0TM20Tchduwr4EaCbmxh1321TABqPGDpS8D/ggOTaljijOA==}
    engines: {node: '>= 10.0.0'}
    cpu: [arm64]
    os: [linux]
    libc: [glibc]

  '@parcel/watcher-linux-arm64-musl@2.5.6':
    resolution: {integrity: sha512-qb6naMDGlbCwdhLj6hgoVKJl2odL34z2sqkC7Z6kzir8b5W65WYDpLB6R06KabvZdgoHI/zxke4b3zR0wAbDTA==}
    engines: {node: '>= 10.0.0'}
    cpu: [arm64]
    os: [linux]
    libc: [musl]

  '@parcel/watcher-linux-x64-glibc@2.5.6':
    resolution: {integrity: sha512-kbT5wvNQlx7NaGjzPFu8nVIW1rWqV780O7ZtkjuWaPUgpv2NMFpjYERVi0UYj1msZNyCzGlaCWEtzc+exjMGbQ==}
    engines: {node: '>= 10.0.0'}
    cpu: [x64]
    os: [linux]
    libc: [glibc]

  '@parcel/watcher-linux-x64-musl@2.5.6':
    resolution: {integrity: sha512-1JRFeC+h7RdXwldHzTsmdtYR/Ku8SylLgTU/reMuqdVD7CtLwf0VR1FqeprZ0eHQkO0vqsbvFLXUmYm/uNKJBg==}
    engines: {node: '>= 10.0.0'}
    cpu: [x64]
    os: [linux]
    libc: [musl]

  '@parcel/watcher-wasm@2.5.6':
    resolution: {integrity: sha512-byAiBZ1t3tXQvc8dMD/eoyE7lTXYorhn+6uVW5AC+JGI1KtJC/LvDche5cfUE+qiefH+Ybq0bUCJU0aB1cSHUA==}
    engines: {node: '>= 10.0.0'}
    bundledDependencies:
      - napi-wasm

  '@parcel/watcher-win32-arm64@2.5.6':
    resolution: {integrity: sha512-3ukyebjc6eGlw9yRt678DxVF7rjXatWiHvTXqphZLvo7aC5NdEgFufVwjFfY51ijYEWpXbqF5jtrK275z52D4Q==}
    engines: {node: '>= 10.0.0'}
    cpu: [arm64]
    os: [win32]

  '@parcel/watcher-win32-ia32@2.5.6':
    resolution: {integrity: sha512-k35yLp1ZMwwee3Ez/pxBi5cf4AoBKYXj00CZ80jUz5h8prpiaQsiRPKQMxoLstNuqe2vR4RNPEAEcjEFzhEz/g==}
    engines: {node: '>= 10.0.0'}
    cpu: [ia32]
    os: [win32]

  '@parcel/watcher-win32-x64@2.5.6':
    resolution: {integrity: sha512-hbQlYcCq5dlAX9Qx+kFb0FHue6vbjlf0FrNzSKdYK2APUf7tGfGxQCk2ihEREmbR6ZMc0MVAD5RIX/41gpUzTw==}
    engines: {node: '>= 10.0.0'}
    cpu: [x64]
    os: [win32]

  '@parcel/watcher@2.5.6':
    resolution: {integrity: sha512-tmmZ3lQxAe/k/+rNnXQRawJ4NjxO2hqiOLTHvWchtGZULp4RyFeh6aU4XdOYBFe2KE1oShQTv4AblOs2iOrNnQ==}
    engines: {node: '>= 10.0.0'}

  '@pkgjs/parseargs@0.11.0':
    resolution: {integrity: sha512-+1VkjdD0QBLPodGrJUeqarH8VAIvQODIbwh9XpP5Syisf7YoQgsJKPNFoqqLQlu+VQ/tVSshMR6loPMn8U+dPg==}
    engines: {node: '>=14'}

  '@polka/url@1.0.0-next.29':
    resolution: {integrity: sha512-wwQAWhWSuHaag8c4q/KN/vCoeOJYshAIvMQwD4GpSb3OiZklFfvAgmj0VCBBImRpuF/aFgIRzllXlVX93Jevww==}

  '@poppinss/colors@4.1.6':
    resolution: {integrity: sha512-H9xkIdFswbS8n1d6vmRd8+c10t2Qe+rZITbbDHHkQixH5+2x1FDGmi/0K+WgWiqQFKPSlIYB7jlH6Kpfn6Fleg==}

  '@poppinss/dumper@0.7.0':
    resolution: {integrity: sha512-0UTYalzk2t6S4rA2uHOz5bSSW2CHdv4vggJI6Alg90yvl0UgXs6XSXpH96OH+bRkX4J/06djv29pqXJ0lq5Kag==}

  '@poppinss/exception@1.2.3':
    resolution: {integrity: sha512-dCED+QRChTVatE9ibtoaxc+WkdzOSjYTKi/+uacHWIsfodVfpsueo3+DKpgU5Px8qXjgmXkSvhXvSCz3fnP9lw==}

  '@rolldown/pluginutils@1.0.0-rc.13':
    resolution: {integrity: sha512-3ngTAv6F/Py35BsYbeeLeecvhMKdsKm4AoOETVhAA+Qc8nrA2I0kF7oa93mE9qnIurngOSpMnQ0x2nQY2FPviA==}

  '@rollup/plugin-alias@6.0.0':
    resolution: {integrity: sha512-tPCzJOtS7uuVZd+xPhoy5W4vThe6KWXNmsFCNktaAh5RTqcLiSfT4huPQIXkgJ6YCOjJHvecOAzQxLFhPxKr+g==}
    engines: {node: '>=20.19.0'}
    peerDependencies:
      rollup: '>=4.0.0'
    peerDependenciesMeta:
      rollup:
        optional: true

  '@rollup/plugin-commonjs@29.0.2':
    resolution: {integrity: sha512-S/ggWH1LU7jTyi9DxZOKyxpVd4hF/OZ0JrEbeLjXk/DFXwRny0tjD2c992zOUYQobLrVkRVMDdmHP16HKP7GRg==}
    engines: {node: '>=16.0.0 || 14 >= 14.17'}
    peerDependencies:
      rollup: ^2.68.0||^3.0.0||^4.0.0
    peerDependenciesMeta:
      rollup:
        optional: true

  '@rollup/plugin-inject@5.0.5':
    resolution: {integrity: sha512-2+DEJbNBoPROPkgTDNe8/1YXWcqxbN5DTjASVIOx8HS+pITXushyNiBV56RB08zuptzz8gT3YfkqriTBVycepg==}
    engines: {node: '>=14.0.0'}
    peerDependencies:
      rollup: ^1.20.0||^2.0.0||^3.0.0||^4.0.0
    peerDependenciesMeta:
      rollup:
        optional: true

  '@rollup/plugin-json@6.1.0':
    resolution: {integrity: sha512-EGI2te5ENk1coGeADSIwZ7G2Q8CJS2sF120T7jLw4xFw9n7wIOXHo+kIYRAoVpJAN+kmqZSoO3Fp4JtoNF4ReA==}
    engines: {node: '>=14.0.0'}
    peerDependencies:
      rollup: ^1.20.0||^2.0.0||^3.0.0||^4.0.0
    peerDependenciesMeta:
      rollup:
        optional: true

  '@rollup/plugin-node-resolve@16.0.3':
    resolution: {integrity: sha512-lUYM3UBGuM93CnMPG1YocWu7X802BrNF3jW2zny5gQyLQgRFJhV1Sq0Zi74+dh/6NBx1DxFC4b4GXg9wUCG5Qg==}
    engines: {node: '>=14.0.0'}
    peerDependencies:
      rollup: ^2.78.0||^3.0.0||^4.0.0
    peerDependenciesMeta:
      rollup:
        optional: true

  '@rollup/plugin-replace@6.0.3':
    resolution: {integrity: sha512-J4RZarRvQAm5IF0/LwUUg+obsm+xZhYnbMXmXROyoSE1ATJe3oXSb9L5MMppdxP2ylNSjv6zFBwKYjcKMucVfA==}
    engines: {node: '>=14.0.0'}
    peerDependencies:
      rollup: ^1.20.0||^2.0.0||^3.0.0||^4.0.0
    peerDependenciesMeta:
      rollup:
        optional: true

  '@rollup/plugin-terser@1.0.0':
    resolution: {integrity: sha512-FnCxhTBx6bMOYQrar6C8h3scPt8/JwIzw3+AJ2K++6guogH5fYaIFia+zZuhqv0eo1RN7W1Pz630SyvLbDjhtQ==}
    engines: {node: '>=20.0.0'}
    peerDependencies:
      rollup: ^2.0.0||^3.0.0||^4.0.0
    peerDependenciesMeta:
      rollup:
        optional: true

  '@rollup/pluginutils@5.3.0':
    resolution: {integrity: sha512-5EdhGZtnu3V88ces7s53hhfK5KSASnJZv8Lulpc04cWO3REESroJXg73DFsOmgbU2BhwV0E20bu2IDZb3VKW4Q==}
    engines: {node: '>=14.0.0'}
    peerDependencies:
      rollup: ^1.20.0||^2.0.0||^3.0.0||^4.0.0
    peerDependenciesMeta:
      rollup:
        optional: true

  '@rollup/rollup-android-arm-eabi@4.60.2':
    resolution: {integrity: sha512-dnlp69efPPg6Uaw2dVqzWRfAWRnYVb1XJ8CyyhIbZeaq4CA5/mLeZ1IEt9QqQxmbdvagjLIm2ZL8BxXv5lH4Yw==}
    cpu: [arm]
    os: [android]

  '@rollup/rollup-android-arm64@4.60.2':
    resolution: {integrity: sha512-OqZTwDRDchGRHHm/hwLOL7uVPB9aUvI0am/eQuWMNyFHf5PSEQmyEeYYheA0EPPKUO/l0uigCp+iaTjoLjVoHg==}
    cpu: [arm64]
    os: [android]

  '@rollup/rollup-darwin-arm64@4.60.2':
    resolution: {integrity: sha512-UwRE7CGpvSVEQS8gUMBe1uADWjNnVgP3Iusyda1nSRwNDCsRjnGc7w6El6WLQsXmZTbLZx9cecegumcitNfpmA==}
    cpu: [arm64]
    os: [darwin]

  '@rollup/rollup-darwin-x64@4.60.2':
    resolution: {integrity: sha512-gjEtURKLCC5VXm1I+2i1u9OhxFsKAQJKTVB8WvDAHF+oZlq0GTVFOlTlO1q3AlCTE/DF32c16ESvfgqR7343/g==}
    cpu: [x64]
    os: [darwin]

  '@rollup/rollup-freebsd-arm64@4.60.2':
    resolution: {integrity: sha512-Bcl6CYDeAgE70cqZaMojOi/eK63h5Me97ZqAQoh77VPjMysA/4ORQBRGo3rRy45x4MzVlU9uZxs8Uwy7ZaKnBw==}
    cpu: [arm64]
    os: [freebsd]

  '@rollup/rollup-freebsd-x64@4.60.2':
    resolution: {integrity: sha512-LU+TPda3mAE2QB0/Hp5VyeKJivpC6+tlOXd1VMoXV/YFMvk/MNk5iXeBfB4MQGRWyOYVJ01625vjkr0Az98OJQ==}
    cpu: [x64]
    os: [freebsd]

  '@rollup/rollup-linux-arm-gnueabihf@4.60.2':
    resolution: {integrity: sha512-2QxQrM+KQ7DAW4o22j+XZ6RKdxjLD7BOWTP0Bv0tmjdyhXSsr2Ul1oJDQqh9Zf5qOwTuTc7Ek83mOFaKnodPjg==}
    cpu: [arm]
    os: [linux]
    libc: [glibc]

  '@rollup/rollup-linux-arm-musleabihf@4.60.2':
    resolution: {integrity: sha512-TbziEu2DVsTEOPif2mKWkMeDMLoYjx95oESa9fkQQK7r/Orta0gnkcDpzwufEcAO2BLBsD7mZkXGFqEdMRRwfw==}
    cpu: [arm]
    os: [linux]
    libc: [musl]

  '@rollup/rollup-linux-arm64-gnu@4.60.2':
    resolution: {integrity: sha512-bO/rVDiDUuM2YfuCUwZ1t1cP+/yqjqz+Xf2VtkdppefuOFS2OSeAfgafaHNkFn0t02hEyXngZkxtGqXcXwO8Rg==}
    cpu: [arm64]
    os: [linux]
    libc: [glibc]

  '@rollup/rollup-linux-arm64-musl@4.60.2':
    resolution: {integrity: sha512-hr26p7e93Rl0Za+JwW7EAnwAvKkehh12BU1Llm9Ykiibg4uIr2rbpxG9WCf56GuvidlTG9KiiQT/TXT1yAWxTA==}
    cpu: [arm64]
    os: [linux]
    libc: [musl]

  '@rollup/rollup-linux-loong64-gnu@4.60.2':
    resolution: {integrity: sha512-pOjB/uSIyDt+ow3k/RcLvUAOGpysT2phDn7TTUB3n75SlIgZzM6NKAqlErPhoFU+npgY3/n+2HYIQVbF70P9/A==}
    cpu: [loong64]
    os: [linux]
    libc: [glibc]

  '@rollup/rollup-linux-loong64-musl@4.60.2':
    resolution: {integrity: sha512-2/w+q8jszv9Ww1c+6uJT3OwqhdmGP2/4T17cu8WuwyUuuaCDDJ2ojdyYwZzCxx0GcsZBhzi3HmH+J5pZNXnd+Q==}
    cpu: [loong64]
    os: [linux]
    libc: [musl]

  '@rollup/rollup-linux-ppc64-gnu@4.60.2':
    resolution: {integrity: sha512-11+aL5vKheYgczxtPVVRhdptAM2H7fcDR5Gw4/bTcteuZBlH4oP9f5s9zYO9aGZvoGeBpqXI/9TZZihZ609wKw==}
    cpu: [ppc64]
    os: [linux]
    libc: [glibc]

  '@rollup/rollup-linux-ppc64-musl@4.60.2':
    resolution: {integrity: sha512-i16fokAGK46IVZuV8LIIwMdtqhin9hfYkCh8pf8iC3QU3LpwL+1FSFGej+O7l3E/AoknL6Dclh2oTdnRMpTzFQ==}
    cpu: [ppc64]
    os: [linux]
    libc: [musl]

  '@rollup/rollup-linux-riscv64-gnu@4.60.2':
    resolution: {integrity: sha512-49FkKS6RGQoriDSK/6E2GkAsAuU5kETFCh7pG4yD/ylj9rKhTmO3elsnmBvRD4PgJPds5W2PkhC82aVwmUcJ7A==}
    cpu: [riscv64]
    os: [linux]
    libc: [glibc]

  '@rollup/rollup-linux-riscv64-musl@4.60.2':
    resolution: {integrity: sha512-mjYNkHPfGpUR00DuM1ZZIgs64Hpf4bWcz9Z41+4Q+pgDx73UwWdAYyf6EG/lRFldmdHHzgrYyge5akFUW0D3mQ==}
    cpu: [riscv64]
    os: [linux]
    libc: [musl]

  '@rollup/rollup-linux-s390x-gnu@4.60.2':
    resolution: {integrity: sha512-ALyvJz965BQk8E9Al/JDKKDLH2kfKFLTGMlgkAbbYtZuJt9LU8DW3ZoDMCtQpXAltZxwBHevXz5u+gf0yA0YoA==}
    cpu: [s390x]
    os: [linux]
    libc: [glibc]

  '@rollup/rollup-linux-x64-gnu@4.60.2':
    resolution: {integrity: sha512-UQjrkIdWrKI626Du8lCQ6MJp/6V1LAo2bOK9OTu4mSn8GGXIkPXk/Vsp4bLHCd9Z9Iz2OTEaokUE90VweJgIYQ==}
    cpu: [x64]
    os: [linux]
    libc: [glibc]

  '@rollup/rollup-linux-x64-musl@4.60.2':
    resolution: {integrity: sha512-bTsRGj6VlSdn/XD4CGyzMnzaBs9bsRxy79eTqTCBsA8TMIEky7qg48aPkvJvFe1HyzQ5oMZdg7AnVlWQSKLTnw==}
    cpu: [x64]
    os: [linux]
    libc: [musl]

  '@rollup/rollup-openbsd-x64@4.60.2':
    resolution: {integrity: sha512-6d4Z3534xitaA1FcMWP7mQPq5zGwBmGbhphh2DwaA1aNIXUu3KTOfwrWpbwI4/Gr0uANo7NTtaykFyO2hPuFLg==}
    cpu: [x64]
    os: [openbsd]

  '@rollup/rollup-openharmony-arm64@4.60.2':
    resolution: {integrity: sha512-NetAg5iO2uN7eB8zE5qrZ3CSil+7IJt4WDFLcC75Ymywq1VZVD6qJ6EvNLjZ3rEm6gB7XW5JdT60c6MN35Z85Q==}
    cpu: [arm64]
    os: [openharmony]

  '@rollup/rollup-win32-arm64-msvc@4.60.2':
    resolution: {integrity: sha512-NCYhOotpgWZ5kdxCZsv6Iudx0wX8980Q/oW4pNFNihpBKsDbEA1zpkfxJGC0yugsUuyDZ7gL37dbzwhR0VI7pQ==}
    cpu: [arm64]
    os: [win32]

  '@rollup/rollup-win32-ia32-msvc@4.60.2':
    resolution: {integrity: sha512-RXsaOqXxfoUBQoOgvmmijVxJnW2IGB0eoMO7F8FAjaj0UTywUO/luSqimWBJn04WNgUkeNhh7fs7pESXajWmkg==}
    cpu: [ia32]
    os: [win32]

  '@rollup/rollup-win32-x64-gnu@4.60.2':
    resolution: {integrity: sha512-qdAzEULD+/hzObedtmV6iBpdL5TIbKVztGiK7O3/KYSf+HIzU257+MX1EXJcyIiDbMAqmbwaufcYPvyRryeZtA==}
    cpu: [x64]
    os: [win32]

  '@rollup/rollup-win32-x64-msvc@4.60.2':
    resolution: {integrity: sha512-Nd/SgG27WoA9e+/TdK74KnHz852TLa94ovOYySo/yMPuTmpckK/jIF2jSwS3g7ELSKXK13/cVdmg1Z/DaCWKxA==}
    cpu: [x64]
    os: [win32]

  '@shikijs/core@4.0.2':
    resolution: {integrity: sha512-hxT0YF4ExEqB8G/qFdtJvpmHXBYJ2lWW7qTHDarVkIudPFE6iCIrqdgWxGn5s+ppkGXI0aEGlibI0PAyzP3zlw==}
    engines: {node: '>=20'}

  '@shikijs/engine-javascript@4.0.2':
    resolution: {integrity: sha512-7PW0Nm49DcoUIQEXlJhNNBHyoGMjalRETTCcjMqEaMoJRLljy1Bi/EGV3/qLBgLKQejdspiiYuHGQW6dX94Nag==}
    engines: {node: '>=20'}

  '@shikijs/engine-oniguruma@4.0.2':
    resolution: {integrity: sha512-UpCB9Y2sUKlS9z8juFSKz7ZtysmeXCgnRF0dlhXBkmQnek7lAToPte8DkxmEYGNTMii72zU/lyXiCB6StuZeJg==}
    engines: {node: '>=20'}

  '@shikijs/langs@4.0.2':
    resolution: {integrity: sha512-KaXby5dvoeuZzN0rYQiPMjFoUrz4hgwIE+D6Du9owcHcl6/g16/yT5BQxSW5cGt2MZBz6Hl0YuRqf12omRfUUg==}
    engines: {node: '>=20'}

  '@shikijs/primitive@4.0.2':
    resolution: {integrity: sha512-M6UMPrSa3fN5ayeJwFVl9qWofl273wtK1VG8ySDZ1mQBfhCpdd8nEx7nPZ/tk7k+TYcpqBZzj/AnwxT9lO+HJw==}
    engines: {node: '>=20'}

  '@shikijs/themes@4.0.2':
    resolution: {integrity: sha512-mjCafwt8lJJaVSsQvNVrJumbnnj1RI8jbUKrPKgE6E3OvQKxnuRoBaYC51H4IGHePsGN/QtALglWBU7DoKDFnA==}
    engines: {node: '>=20'}

  '@shikijs/transformers@4.0.2':
    resolution: {integrity: sha512-1+L0gf9v+SdDXs08vjaLb3mBFa8U7u37cwcBQIv/HCocLwX69Tt6LpUCjtB+UUTvQxI7BnjZKhN/wMjhHBcJGg==}
    engines: {node: '>=20'}

  '@shikijs/types@4.0.2':
    resolution: {integrity: sha512-qzbeRooUTPnLE+sHD/Z8DStmaDgnbbc/pMrU203950aRqjX/6AFHeDYT+j00y2lPdz0ywJKx7o/7qnqTivtlXg==}
    engines: {node: '>=20'}

  '@shikijs/vscode-textmate@10.0.2':
    resolution: {integrity: sha512-83yeghZ2xxin3Nj8z1NMd/NCuca+gsYXswywDy5bHvwlWL8tpTQmzGeUuHd9FC3E/SBEMvzJRwWEOz5gGes9Qg==}

  '@sindresorhus/base62@1.0.0':
    resolution: {integrity: sha512-TeheYy0ILzBEI/CO55CP6zJCSdSWeRtGnHy8U8dWSUH4I68iqTsy7HkMktR4xakThc9jotkPQUXT4ITdbV7cHA==}
    engines: {node: '>=18'}

  '@sindresorhus/is@4.6.0':
    resolution: {integrity: sha512-t09vSN3MdfsyCHoFcTRCH/iUtG7OJ0CsjzB8cjAmKc/va/kIgeDI/TxsigdncE/4be734m0cvIYwNaV4i2XqAw==}
    engines: {node: '>=10'}

  '@sindresorhus/is@7.2.0':
    resolution: {integrity: sha512-P1Cz1dWaFfR4IR+U13mqqiGsLFf1KbayybWwdd2vfctdV6hDpUkgCY0nKOLLTMSoRd/jJNjtbqzf13K8DCCXQw==}
    engines: {node: '>=18'}

  '@sindresorhus/merge-streams@4.0.0':
    resolution: {integrity: sha512-tlqY9xq5ukxTUZBmoOp+m61cqwQD5pHJtFY3Mn8CA8ps6yghLH/Hw8UPdqg4OLmFW3IFlcXnQNmo/dh8HzXYIQ==}
    engines: {node: '>=18'}

  '@socket.io/component-emitter@3.1.2':
    resolution: {integrity: sha512-9BCxFwvbGg/RsZK9tjXd8s4UcwR0MWeFQ1XEKIQVVvAGJyINdrqKMcTRyLoK8Rse1GjzLV9cwjWV1olXRWEXVA==}

  '@speed-highlight/core@1.2.14':
    resolution: {integrity: sha512-G4ewlBNhUtlLvrJTb88d2mdy2KRijzs4UhnlrOSRT4bmjh/IqNElZa3zkrZ+TC47TwtlDWzVLFADljF1Ijp5hA==}

  '@sqlite.org/sqlite-wasm@3.50.4-build1':
    resolution: {integrity: sha512-Qig2Wso7gPkU1PtXwFzndh+CTRzrIFxVGqv6eCetjU7YqxlHItj+GvQYwYTppCRgAPawtRN/4AJcEgB9xDHGug==}
    hasBin: true

  '@standard-schema/spec@1.1.0':
    resolution: {integrity: sha512-l2aFy5jALhniG5HgqrD6jXLi/rUWrKvqN/qJx6yoJsgKhblVd+iqqU4RCXavm/jPityDo5TCvKMnpjKnOriy0w==}

  '@stylistic/eslint-plugin@5.10.0':
    resolution: {integrity: sha512-nPK52ZHvot8Ju/0A4ucSX1dcPV2/1clx0kLcH5wDmrE4naKso7TUC/voUyU1O9OTKTrR6MYip6LP0ogEMQ9jPQ==}
    engines: {node: ^18.18.0 || ^20.9.0 || >=21.1.0}
    peerDependencies:
      eslint: ^9.0.0 || ^10.0.0

  '@swc/helpers@0.5.19':
    resolution: {integrity: sha512-QamiFeIK3txNjgUTNppE6MiG3p7TdninpZu0E0PbqVh1a9FNLT2FRhisaa4NcaX52XVhA5l7Pk58Ft7Sqi/2sA==}

  '@tailwindcss/node@4.2.4':
    resolution: {integrity: sha512-Ai7+yQPxz3ddrDQzFfBKdHEVBg0w3Zl83jnjuwxnZOsnH9pGn93QHQtpU0p/8rYWxvbFZHneni6p1BSLK4DkGA==}

  '@tailwindcss/oxide-android-arm64@4.2.4':
    resolution: {integrity: sha512-e7MOr1SAn9U8KlZzPi1ZXGZHeC5anY36qjNwmZv9pOJ8E4Q6jmD1vyEHkQFmNOIN7twGPEMXRHmitN4zCMN03g==}
    engines: {node: '>= 20'}
    cpu: [arm64]
    os: [android]

  '@tailwindcss/oxide-darwin-arm64@4.2.4':
    resolution: {integrity: sha512-tSC/Kbqpz/5/o/C2sG7QvOxAKqyd10bq+ypZNf+9Fi2TvbVbv1zNpcEptcsU7DPROaSbVgUXmrzKhurFvo5eDg==}
    engines: {node: '>= 20'}
    cpu: [arm64]
    os: [darwin]

  '@tailwindcss/oxide-darwin-x64@4.2.4':
    resolution: {integrity: sha512-yPyUXn3yO/ufR6+Kzv0t4fCg2qNr90jxXc5QqBpjlPNd0NqyDXcmQb/6weunH/MEDXW5dhyEi+agTDiqa3WsGg==}
    engines: {node: '>= 20'}
    cpu: [x64]
    os: [darwin]

  '@tailwindcss/oxide-freebsd-x64@4.2.4':
    resolution: {integrity: sha512-BoMIB4vMQtZsXdGLVc2z+P9DbETkiopogfWZKbWwM8b/1Vinbs4YcUwo+kM/KeLkX3Ygrf4/PsRndKaYhS8Eiw==}
    engines: {node: '>= 20'}
    cpu: [x64]
    os: [freebsd]

  '@tailwindcss/oxide-linux-arm-gnueabihf@4.2.4':
    resolution: {integrity: sha512-7pIHBLTHYRAlS7V22JNuTh33yLH4VElwKtB3bwchK/UaKUPpQ0lPQiOWcbm4V3WP2I6fNIJ23vABIvoy2izdwA==}
    engines: {node: '>= 20'}
    cpu: [arm]
    os: [linux]

  '@tailwindcss/oxide-linux-arm64-gnu@4.2.4':
    resolution: {integrity: sha512-+E4wxJ0ZGOzSH325reXTWB48l42i93kQqMvDyz5gqfRzRZ7faNhnmvlV4EPGJU3QJM/3Ab5jhJ5pCRUsKn6OQw==}
    engines: {node: '>= 20'}
    cpu: [arm64]
    os: [linux]
    libc: [glibc]

  '@tailwindcss/oxide-linux-arm64-musl@4.2.4':
    resolution: {integrity: sha512-bBADEGAbo4ASnppIziaQJelekCxdMaxisrk+fB7Thit72IBnALp9K6ffA2G4ruj90G9XRS2VQ6q2bCKbfFV82g==}
    engines: {node: '>= 20'}
    cpu: [arm64]
    os: [linux]
    libc: [musl]

  '@tailwindcss/oxide-linux-x64-gnu@4.2.4':
    resolution: {integrity: sha512-7Mx25E4WTfnht0TVRTyC00j3i0M+EeFe7wguMDTlX4mRxafznw0CA8WJkFjWYH5BlgELd1kSjuU2JiPnNZbJDA==}
    engines: {node: '>= 20'}
    cpu: [x64]
    os: [linux]
    libc: [glibc]

  '@tailwindcss/oxide-linux-x64-musl@4.2.4':
    resolution: {integrity: sha512-2wwJRF7nyhOR0hhHoChc04xngV3iS+akccHTGtz965FwF0up4b2lOdo6kI1EbDaEXKgvcrFBYcYQQ/rrnWFVfA==}
    engines: {node: '>= 20'}
    cpu: [x64]
    os: [linux]
    libc: [musl]

  '@tailwindcss/oxide-wasm32-wasi@4.2.4':
    resolution: {integrity: sha512-FQsqApeor8Fo6gUEklzmaa9994orJZZDBAlQpK2Mq+DslRKFJeD6AjHpBQ0kZFQohVr8o85PPh8eOy86VlSCmw==}
    engines: {node: '>=14.0.0'}
    cpu: [wasm32]
    bundledDependencies:
      - '@napi-rs/wasm-runtime'
      - '@emnapi/core'
      - '@emnapi/runtime'
      - '@tybys/wasm-util'
      - '@emnapi/wasi-threads'
      - tslib

  '@tailwindcss/oxide-win32-arm64-msvc@4.2.4':
    resolution: {integrity: sha512-L9BXqxC4ToVgwMFqj3pmZRqyHEztulpUJzCxUtLjobMCzTPsGt1Fa9enKbOpY2iIyVtaHNeNvAK8ERP/64sqGQ==}
    engines: {node: '>= 20'}
    cpu: [arm64]
    os: [win32]

  '@tailwindcss/oxide-win32-x64-msvc@4.2.4':
    resolution: {integrity: sha512-ESlKG0EpVJQwRjXDDa9rLvhEAh0mhP1sF7sap9dNZT0yyl9SAG6T7gdP09EH0vIv0UNTlo6jPWyujD6559fZvw==}
    engines: {node: '>= 20'}
    cpu: [x64]
    os: [win32]

  '@tailwindcss/oxide@4.2.4':
    resolution: {integrity: sha512-9El/iI069DKDSXwTvB9J4BwdO5JhRrOweGaK25taBAvBXyXqJAX+Jqdvs8r8gKpsI/1m0LeJLyQYTf/WLrBT1Q==}
    engines: {node: '>= 20'}

  '@tailwindcss/postcss@4.2.4':
    resolution: {integrity: sha512-wgAVj6nUWAolAu8YFvzT2cTBIElWHkjZwFYovF+xsqKsW2ADxM/X2opxj5NsF/qVccAOjRNe8X2IdPzMsWyHTg==}

  '@tailwindcss/vite@4.2.4':
    resolution: {integrity: sha512-pCvohwOCspk3ZFn6eJzrrX3g4n2JY73H6MmYC87XfGPyTty4YsCjYTMArRZm/zOI8dIt3+EcrLHAFPe5A4bgtw==}
    peerDependencies:
      vite: ^5.2.0 || ^6 || ^7 || ^8

  '@tanstack/table-core@8.21.3':
    resolution: {integrity: sha512-ldZXEhOBb8Is7xLs01fR3YEc3DERiz5silj8tnGkFZytt1abEvl/GhUmCE0PMLaMPTa3Jk4HbKmRlHmu+gCftg==}
    engines: {node: '>=12'}

  '@tanstack/virtual-core@3.14.0':
    resolution: {integrity: sha512-JLANqGy/D6k4Ujmh8Tr25lGimuOXNiaVyXaCAZS0W+1390sADdGnyUdSWNIfd49gebtIxGMij4IktRVzrdr12Q==}

  '@tanstack/vue-table@8.21.3':
    resolution: {integrity: sha512-rusRyd77c5tDPloPskctMyPLFEQUeBzxdQ+2Eow4F7gDPlPOB1UnnhzfpdvqZ8ZyX2rRNGmqNnQWm87OI2OQPw==}
    engines: {node: '>=12'}
    peerDependencies:
      vue: '>=3.2'

  '@tanstack/vue-virtual@3.13.24':
    resolution: {integrity: sha512-A0k2qF0zFSUStXSZkGXABouXr2Tw2Ztl/cVIYG9qy84uR8W7UNjAcX3DvzBS3YnDcwvLxab8v7dbmYBZ39itDA==}
    peerDependencies:
      vue: ^2.7.0 || ^3.0.0

  '@tiptap/core@3.22.4':
    resolution: {integrity: sha512-vGIGm/HpqLg8EAAQXQ+koV+/S828OEpzocfWcPOwo1u2QUVf9dQG47Yy6JJ8zFFaJwfv4dBcOXli+7BrJwsxDQ==}
    peerDependencies:
      '@tiptap/pm': 3.22.4

  '@tiptap/extension-blockquote@3.22.4':
    resolution: {integrity: sha512-7/61kNPbGFhMgM//zMknD0pSb69rGdRIkpulXOWS1JBrFHkH6hjZDfrOETNzgKkO+NlmzVl9rXSTv0xauS3lzA==}
    peerDependencies:
      '@tiptap/core': 3.22.4

  '@tiptap/extension-bold@3.22.4':
    resolution: {integrity: sha512-jIaPKfNOQu2lhpbLDvtwlQqM+mjF+Kk+auHpzYjBnsuwUli1Cl5ZOau7RH+rru/SQvZe1DtpQlANujDywugZAA==}
    peerDependencies:
      '@tiptap/core': 3.22.4

  '@tiptap/extension-bubble-menu@3.22.4':
    resolution: {integrity: sha512-v4pux5Ql3THAEjaLMY4ldtdy/Xy2qU7PJLBkq8ugLp8qicaKC+tpqxp6sGif4vLIjz7Ap5hurRbTNbXzszyyHA==}
    peerDependencies:
      '@tiptap/core': 3.22.4
      '@tiptap/pm': 3.22.4

  '@tiptap/extension-bullet-list@3.22.4':
    resolution: {integrity: sha512-TB+d3fGcTixYjO7coKqTr1mGTJuqr8hjDCPUFgzuvKyJnBhqWITmBzQ/8CLq4rr6mihgGURbD3N+xkQuPAKFiw==}
    peerDependencies:
      '@tiptap/extension-list': 3.22.4

  '@tiptap/extension-code-block@3.22.4':
    resolution: {integrity: sha512-MEurzNXfMET3rhjpoPJYUgMfxTdTqbzT9+ToFrqNGAHocdXVm6m1hhO2frVC7fEtHPnxXKsn0Z3NUbCRkRTLuA==}
    peerDependencies:
      '@tiptap/core': 3.22.4
      '@tiptap/pm': 3.22.4

  '@tiptap/extension-code@3.22.4':
    resolution: {integrity: sha512-cnbxmVhAcc7X3G81QUYEmKP0ve2hRmvAiFXBuuv9RUtQlBiRnzmhHoJOMgkX0CsMR7+8kMRpTfeDUYq2xp5s5w==}
    peerDependencies:
      '@tiptap/core': 3.22.4

  '@tiptap/extension-collaboration@3.22.4':
    resolution: {integrity: sha512-4g4DdpvXZyYYCcWs3cO4DwtzhukqI13waYUKfwOcNnQwZ4YOCR83ET/kgqMk/xMAfbymKghbyAZRCc33zD5xvw==}
    peerDependencies:
      '@tiptap/core': 3.22.4
      '@tiptap/pm': 3.22.4
      '@tiptap/y-tiptap': ^3.0.2
      yjs: ^13

  '@tiptap/extension-document@3.22.4':
    resolution: {integrity: sha512-XQKla1+703FqQJC48tPDVgt9ucGiFbIEmQdOg5L5o07z9a6/NzuaZAc+1zJ7NxcUZzy+z6wBn1PrVMTiqiSXlw==}
    peerDependencies:
      '@tiptap/core': 3.22.4

  '@tiptap/extension-drag-handle-vue-3@3.22.4':
    resolution: {integrity: sha512-ySedk/4Szd8M3t2yE+5tjfXyTIwanmQ51jIGxro23D383upDxD0c/lrTk+9+KUWJfsUTqOrJDrzogpRF+F30dQ==}
    peerDependencies:
      '@tiptap/extension-drag-handle': 3.22.4
      '@tiptap/pm': 3.22.4
      '@tiptap/vue-3': 3.22.4
      vue: ^3.0.0

  '@tiptap/extension-drag-handle@3.22.4':
    resolution: {integrity: sha512-VCheiqy0OGrcrxOYt7Kp7MXWMZoEaZp517HnRrdrvcCCO0j2hcrT5mbo1mMPzP/WvTUHkXCmqcLv+uIk3Bdo/g==}
    peerDependencies:
      '@tiptap/core': 3.22.4
      '@tiptap/extension-collaboration': 3.22.4
      '@tiptap/extension-node-range': 3.22.4
      '@tiptap/pm': 3.22.4
      '@tiptap/y-tiptap': ^3.0.2

  '@tiptap/extension-dropcursor@3.22.4':
    resolution: {integrity: sha512-N9/yMDC35jJp0V/naL0+6gi4gUDUIcPpWEzFdCDWUSYBA8mt41c1kI1ZU7UTKYIBzTClenhYHRc2XKZxxx0+LQ==}
    peerDependencies:
      '@tiptap/extensions': 3.22.4

  '@tiptap/extension-floating-menu@3.22.4':
    resolution: {integrity: sha512-DFuyYxgaZPgxum5z1yvJPbfYCvDdO8geXsdyqt0qYYdiat3aGE4ncJhiLRIFDhSHBhaZg5eCgu/YPYAN6jZnrA==}
    peerDependencies:
      '@floating-ui/dom': ^1.0.0
      '@tiptap/core': 3.22.4
      '@tiptap/pm': 3.22.4

  '@tiptap/extension-gapcursor@3.22.4':
    resolution: {integrity: sha512-UYBEUj3SFpKINIE7AdzcyeS3xICK+ee+YLBbuqNXyHStYChjJOohzJehqiqhjR16A88KQQ+ZjgyDcItKGygSog==}
    peerDependencies:
      '@tiptap/extensions': 3.22.4

  '@tiptap/extension-hard-break@3.22.4':
    resolution: {integrity: sha512-xq+a4dE7T6VwApCkh/yU3p30gn3F8g8Arb9CyEZm58/WIJUIGvHSTjDdHmvU16+kiWSBg+wOOsaFHhYjJjxcKA==}
    peerDependencies:
      '@tiptap/core': 3.22.4

  '@tiptap/extension-heading@3.22.4':
    resolution: {integrity: sha512-TUaj5f0Ir5qy9HKKt2ocnwfXKpZDYeHgbbP9gshKFzdq5PLe1RbIgkjfy6bnoI865cYjmPYWRjcT7XsKyIcb9Q==}
    peerDependencies:
      '@tiptap/core': 3.22.4

  '@tiptap/extension-horizontal-rule@3.22.4':
    resolution: {integrity: sha512-cCI1HekGQwhY/MbgaKQ0R/7HcH5ZM1oFAyI/J72QGLC0XnF403S/OXoHMuBWr1mCu8hNiQWCzeNRJUty0iytNw==}
    peerDependencies:
      '@tiptap/core': 3.22.4
      '@tiptap/pm': 3.22.4

  '@tiptap/extension-image@3.22.4':
    resolution: {integrity: sha512-ZDc+fLaratTQ4IgnKcJJwfUgUgpcHjbZSBi6UQAILJwkflMy1Zxj8mpbma5P934nLSI+uDnR5ret6ZZLNITKhA==}
    peerDependencies:
      '@tiptap/core': 3.22.4

  '@tiptap/extension-italic@3.22.4':
    resolution: {integrity: sha512-fVSDx5AYXgDI3v2zZIqb7V8EewthwM2NJ/ZCX+XaxRsqNEpnjVhgHs7UlvDqK1wj2OJ6zmUNjPtVlAFRxwT+HQ==}
    peerDependencies:
      '@tiptap/core': 3.22.4

  '@tiptap/extension-link@3.22.4':
    resolution: {integrity: sha512-uoP3yus02uwGPVzW2QaEPJWVIrUb/r5nKm6c8DiJv9fNSX1+gykZZMg42c6GwRFLZ/vyfWjVCbAE03VMUqafgA==}
    peerDependencies:
      '@tiptap/core': 3.22.4
      '@tiptap/pm': 3.22.4

  '@tiptap/extension-list-item@3.22.4':
    resolution: {integrity: sha512-H659KXTvggSypIDWSOJBZ37jh9pKjQriDDvYPYvOZCdfij0D0hsDXN/wXoypArneUkoBdgruHfTtMkFOaQlgkw==}
    peerDependencies:
      '@tiptap/extension-list': 3.22.4

  '@tiptap/extension-list-keymap@3.22.4':
    resolution: {integrity: sha512-t/zhker4oIS78AIGYDdFFfZC6zSBlszfD7z/zqFLGCg5PHNNgkZK5hKj6Vyix6D2SapRn/ajnx+8mhbKIUH5eA==}
    peerDependencies:
      '@tiptap/extension-list': 3.22.4

  '@tiptap/extension-list@3.22.4':
    resolution: {integrity: sha512-Xe8UFvvHmyp/c/TJsFwlwU9CWACYbBirNsluJ3U1+H8BTu1wqdrT/AXR5uIXeyCl5kiWKgX5q71eHWbYFOrqrg==}
    peerDependencies:
      '@tiptap/core': 3.22.4
      '@tiptap/pm': 3.22.4

  '@tiptap/extension-mention@3.22.4':
    resolution: {integrity: sha512-ZUJ1gCZlH+JGTAT7lVpZjcMAzvIi9hXIyBjOmjL+737NlF+Cfgo+fjHqFQgOSsiO9LEyc3ZMSclmbzII1Jy6IQ==}
    peerDependencies:
      '@tiptap/core': 3.22.4
      '@tiptap/pm': 3.22.4
      '@tiptap/suggestion': 3.22.4

  '@tiptap/extension-node-range@3.22.4':
    resolution: {integrity: sha512-AJgZPX9DLDjN1nE4WLQBPHRChxrV3JuWHF6OakZIdO23cuBcg233FCQTqHQ/eNS/tD3J+Kw9gBc4ZUDhBes9gg==}
    peerDependencies:
      '@tiptap/core': 3.22.4
      '@tiptap/pm': 3.22.4

  '@tiptap/extension-ordered-list@3.22.4':
    resolution: {integrity: sha512-w77hPVf7pcHt97vfrybg/l0t5CimCd4y75OJKuHuo3CfgM5xbUP/gaPNMDyLLe7MYole/UHi/XvG3XjgzqTzAw==}
    peerDependencies:
      '@tiptap/extension-list': 3.22.4

  '@tiptap/extension-paragraph@3.22.4':
    resolution: {integrity: sha512-de6dFkIhigiENESY6rNJ3yTVS/337ybfP30dNPudTwGe9oAu9ZCS+04j6QCvXSjhlI3ULiv7wiSHqrP26Gd+Hw==}
    peerDependencies:
      '@tiptap/core': 3.22.4

  '@tiptap/extension-placeholder@3.22.4':
    resolution: {integrity: sha512-Z3wtWL+KufwkC7CkJge5enAxx4q8C3oOYixme02snY9zfjX3V/1pjAmEfP4wxScgM5GIuTEJ83B9Yz3wRzPA6Q==}
    peerDependencies:
      '@tiptap/extensions': 3.22.4

  '@tiptap/extension-strike@3.22.4':
    resolution: {integrity: sha512-aRHWQj42HiailXSC9LkKYM3jWMcSeGwOjbqM4PiuxQZmHVDRFmeHkfJItOdn2cSHaO0vuEVK+TvrWUWsBFi3pg==}
    peerDependencies:
      '@tiptap/core': 3.22.4

  '@tiptap/extension-text@3.22.4':
    resolution: {integrity: sha512-mM69uUW5cSxIhyEpWXi/YcfyupcJMDLCPEfYi62awH0iOP/LRoCv/nHjJq4Hyj/KxRJbe8HKwIUnqaCUf7m5Pg==}
    peerDependencies:
      '@tiptap/core': 3.22.4

  '@tiptap/extension-underline@3.22.4':
    resolution: {integrity: sha512-08kGdbhIrA6h10GWXqOkqIveaBj5tmxclK208/nUIAlonI9hPd739vu7fmVtpnmqCnSSNpoRtU4u6Gj5at0ZpA==}
    peerDependencies:
      '@tiptap/core': 3.22.4

  '@tiptap/extensions@3.22.4':
    resolution: {integrity: sha512-fOe8VptJvLPs32bNdUYo8SRyljwqKNQVXWW056VoXIc5en/59OdJlJQVeHI0jRRciH3MtrqODi/gfJR0VHNZ8A==}
    peerDependencies:
      '@tiptap/core': 3.22.4
      '@tiptap/pm': 3.22.4

  '@tiptap/markdown@3.22.4':
    resolution: {integrity: sha512-gcoLOq5TBntw13QdeWMy7yc2X+b9yTplcFb5kpMQNgNoxlu0+jlX4LiBR+E6lOV+m+AtkprHHltTYyKG23bdOw==}
    peerDependencies:
      '@tiptap/core': 3.22.4
      '@tiptap/pm': 3.22.4

  '@tiptap/pm@3.22.4':
    resolution: {integrity: sha512-hj8Qka6WcHRllHUdeSjDnq2XaisUo4KsoGJc1WcFpoa1Yd+OeD861zUMnV7DFVGdZRy45Obht0CUYJpXQ4yA4w==}

  '@tiptap/starter-kit@3.22.4':
    resolution: {integrity: sha512-qWjw+vfdin1rzMRpRU4cC5tLTwMJtUpXeQukv+6mOqqvhptuwuZBjUHImVEJaSPoHXS7+1ut+nTnrLyWyEuE5Q==}

  '@tiptap/suggestion@3.22.4':
    resolution: {integrity: sha512-1buvLZemITTeKmPf2wGFWvvhRFKjdQ+JgMqc67xBraOKeDd8wQi1e2XlhCYAtlVMm5f6j+qlLC/MvwuHI2jHeQ==}
    peerDependencies:
      '@tiptap/core': 3.22.4
      '@tiptap/pm': 3.22.4

  '@tiptap/vue-3@3.22.4':
    resolution: {integrity: sha512-fcqUWt6LlA5PbcFaDXyV1apWwAs8j80m0kWwoL5+DgKdkGxsB5LgDZU1pTWle0zvR5zmGvJ7LmB6EGAYIBjdmQ==}
    peerDependencies:
      '@floating-ui/dom': ^1.0.0
      '@tiptap/core': 3.22.4
      '@tiptap/pm': 3.22.4
      vue: ^3.0.0

  '@tiptap/y-tiptap@3.0.2':
    resolution: {integrity: sha512-flMn/YW6zTbc6cvDaUPh/NfLRTXDIqgpBUkYzM74KA1snqQwhOMjnRcnpu4hDFrTnPO6QGzr99vRyXEA7M44WA==}
    engines: {node: '>=16.0.0', npm: '>=8.0.0'}
    peerDependencies:
      prosemirror-model: ^1.7.1
      prosemirror-state: ^1.2.3
      prosemirror-view: ^1.9.10
      y-protocols: ^1.0.1
      yjs: ^13.5.38

  '@tybys/wasm-util@0.10.1':
    resolution: {integrity: sha512-9tTaPJLSiejZKx+Bmog4uSubteqTvFrVrURwkmHixBo0G4seD0zUxp98E1DzUBJxLQ3NPwXrGKDiVjwx/DpPsg==}

  '@types/debug@4.1.12':
    resolution: {integrity: sha512-vIChWdVG3LG1SMxEvI/AK+FWJthlrqlTu7fbrlywTkkaONwk/UAGaULXRlf8vkzFBLVm0zkMdCquhL5aOjhXPQ==}

  '@types/esrecurse@4.3.1':
    resolution: {integrity: sha512-xJBAbDifo5hpffDBuHl0Y8ywswbiAp/Wi7Y/GtAgSlZyIABppyurxVueOPE8LUQOxdlgi6Zqce7uoEpqNTeiUw==}

  '@types/estree@1.0.8':
    resolution: {integrity: sha512-dWHzHa2WqEXI/O1E9OjrocMTKJl2mSrEolh1Iomrv6U+JuNwaHXsXx9bLu5gG7BUWFIN0skIQJQ/L1rIex4X6w==}

  '@types/hast@3.0.4':
    resolution: {integrity: sha512-WPs+bbQw5aCj+x6laNGWLH3wviHtoCv/P3+otBhbOhJgG8qtpdAMlTCxLtsTWA7LH1Oh/bFCHsBn0TPS5m30EQ==}

  '@types/json-schema@7.0.15':
    resolution: {integrity: sha512-5+fP8P8MFNC+AyZCDxrB2pkZFPGzqQWUzpSeuuVLvm8VMcorNYavBqoFcxK8bQz4Qsbn4oUEEem4wDLfcysGHA==}

  '@types/mdast@4.0.4':
    resolution: {integrity: sha512-kGaNbPh1k7AFzgpud/gMdvIm5xuECykRR+JnWKQno9TAXVa6WIVCGTPvYGekIDL4uwCZQSYbUxNBSb1aUo79oA==}

  '@types/ms@2.1.0':
    resolution: {integrity: sha512-GsCCIZDE/p3i96vtEqx+7dBUGXrc7zeSK3wwPHIaRThS+9OhWIXRqzs4d6k1SVU8g91DrNRWxWUGhp5KXQb2VA==}

  '@types/node@25.5.0':
    resolution: {integrity: sha512-jp2P3tQMSxWugkCUKLRPVUpGaL5MVFwF8RDuSRztfwgN1wmqJeMSbKlnEtQqU8UrhTmzEmZdu2I6v2dpp7XIxw==}

  '@types/parse-path@7.1.0':
    resolution: {integrity: sha512-EULJ8LApcVEPbrfND0cRQqutIOdiIgJ1Mgrhpy755r14xMohPTEpkV/k28SJvuOs9bHRFW8x+KeDAEPiGQPB9Q==}
    deprecated: This is a stub types definition. parse-path provides its own type definitions, so you do not need this installed.

  '@types/resolve@1.20.2':
    resolution: {integrity: sha512-60BCwRFOZCQhDncwQdxxeOEEkbc5dIMccYLwbxsS4TUNeVECQ/pBJ0j09mrHOl/JJvpRPGwO9SvE4nR2Nb/a4Q==}

  '@types/unist@2.0.11':
    resolution: {integrity: sha512-CmBKiL6NNo/OqgmMn95Fk9Whlp2mtvIv+KNpQKN2F4SjvrEesubTRWGYSg+BnWZOnlCaSTU1sMpsBOzgbYhnsA==}

  '@types/unist@3.0.3':
    resolution: {integrity: sha512-ko/gIFJRv177XgZsZcBwnqJN5x/Gien8qNOn0D5bQU/zAzVf9Zt3BlcUiLqhV9y4ARk0GbT3tnUiPNgnTXzc/Q==}

  '@types/web-bluetooth@0.0.20':
    resolution: {integrity: sha512-g9gZnnXVq7gM7v3tJCWV/qw7w+KeOlSHAhgF9RytFyifW6AF61hdT2ucrYhPq9hLs5JIryeupHV3qGk95dH9ow==}

  '@types/web-bluetooth@0.0.21':
    resolution: {integrity: sha512-oIQLCGWtcFZy2JW77j9k8nHzAOpqMHLQejDA48XXMWH6tjCQHz5RCFz1bzsmROyL6PUm+LLnUiI4BCn221inxA==}

  '@typescript-eslint/eslint-plugin@8.57.0':
    resolution: {integrity: sha512-qeu4rTHR3/IaFORbD16gmjq9+rEs9fGKdX0kF6BKSfi+gCuG3RCKLlSBYzn/bGsY9Tj7KE/DAQStbp8AHJGHEQ==}
    engines: {node: ^18.18.0 || ^20.9.0 || >=21.1.0}
    peerDependencies:
      '@typescript-eslint/parser': ^8.57.0
      eslint: ^8.57.0 || ^9.0.0 || ^10.0.0
      typescript: '>=4.8.4 <6.0.0'

  '@typescript-eslint/parser@8.57.0':
    resolution: {integrity: sha512-XZzOmihLIr8AD1b9hL9ccNMzEMWt/dE2u7NyTY9jJG6YNiNthaD5XtUHVF2uCXZ15ng+z2hT3MVuxnUYhq6k1g==}
    engines: {node: ^18.18.0 || ^20.9.0 || >=21.1.0}
    peerDependencies:
      eslint: ^8.57.0 || ^9.0.0 || ^10.0.0
      typescript: '>=4.8.4 <6.0.0'

  '@typescript-eslint/project-service@8.57.0':
    resolution: {integrity: sha512-pR+dK0BlxCLxtWfaKQWtYr7MhKmzqZxuii+ZjuFlZlIGRZm22HnXFqa2eY+90MUz8/i80YJmzFGDUsi8dMOV5w==}
    engines: {node: ^18.18.0 || ^20.9.0 || >=21.1.0}
    peerDependencies:
      typescript: '>=4.8.4 <6.0.0'

  '@typescript-eslint/scope-manager@8.57.0':
    resolution: {integrity: sha512-nvExQqAHF01lUM66MskSaZulpPL5pgy5hI5RfrxviLgzZVffB5yYzw27uK/ft8QnKXI2X0LBrHJFr1TaZtAibw==}
    engines: {node: ^18.18.0 || ^20.9.0 || >=21.1.0}

  '@typescript-eslint/tsconfig-utils@8.57.0':
    resolution: {integrity: sha512-LtXRihc5ytjJIQEH+xqjB0+YgsV4/tW35XKX3GTZHpWtcC8SPkT/d4tqdf1cKtesryHm2bgp6l555NYcT2NLvA==}
    engines: {node: ^18.18.0 || ^20.9.0 || >=21.1.0}
    peerDependencies:
      typescript: '>=4.8.4 <6.0.0'

  '@typescript-eslint/type-utils@8.57.0':
    resolution: {integrity: sha512-yjgh7gmDcJ1+TcEg8x3uWQmn8ifvSupnPfjP21twPKrDP/pTHlEQgmKcitzF/rzPSmv7QjJ90vRpN4U+zoUjwQ==}
    engines: {node: ^18.18.0 || ^20.9.0 || >=21.1.0}
    peerDependencies:
      eslint: ^8.57.0 || ^9.0.0 || ^10.0.0
      typescript: '>=4.8.4 <6.0.0'

  '@typescript-eslint/types@8.57.0':
    resolution: {integrity: sha512-dTLI8PEXhjUC7B9Kre+u0XznO696BhXcTlOn0/6kf1fHaQW8+VjJAVHJ3eTI14ZapTxdkOmc80HblPQLaEeJdg==}
    engines: {node: ^18.18.0 || ^20.9.0 || >=21.1.0}

  '@typescript-eslint/typescript-estree@8.57.0':
    resolution: {integrity: sha512-m7faHcyVg0BT3VdYTlX8GdJEM7COexXxS6KqGopxdtkQRvBanK377QDHr4W/vIPAR+ah9+B/RclSW5ldVniO1Q==}
    engines: {node: ^18.18.0 || ^20.9.0 || >=21.1.0}
    peerDependencies:
      typescript: '>=4.8.4 <6.0.0'

  '@typescript-eslint/utils@8.57.0':
    resolution: {integrity: sha512-5iIHvpD3CZe06riAsbNxxreP+MuYgVUsV0n4bwLH//VJmgtt54sQeY2GszntJ4BjYCpMzrfVh2SBnUQTtys2lQ==}
    engines: {node: ^18.18.0 || ^20.9.0 || >=21.1.0}
    peerDependencies:
      eslint: ^8.57.0 || ^9.0.0 || ^10.0.0
      typescript: '>=4.8.4 <6.0.0'

  '@typescript-eslint/visitor-keys@8.57.0':
    resolution: {integrity: sha512-zm6xx8UT/Xy2oSr2ZXD0pZo7Jx2XsCoID2IUh9YSTFRu7z+WdwYTRk6LhUftm1crwqbuoF6I8zAFeCMw0YjwDg==}
    engines: {node: ^18.18.0 || ^20.9.0 || >=21.1.0}

  '@ungap/structured-clone@1.3.0':
    resolution: {integrity: sha512-WmoN8qaIAo7WTYWbAZuG8PYEhn5fkz7dZrqTBZ7dtt//lL2Gwms1IcnQ5yHqjDfX8Ft5j4YzDM23f87zBfDe9g==}
    deprecated: Potential CWE-502 - Update to 1.3.1 or higher

  '@unhead/vue@2.1.13':
    resolution: {integrity: sha512-HYy0shaHRnLNW9r85gppO8IiGz0ONWVV3zGdlT8CQ0tbTwixznJCIiyqV4BSV1aIF1jJIye0pd1p/k6Eab8Z/A==}
    peerDependencies:
      vue: '>=3.5.18'

  '@unrs/resolver-binding-android-arm-eabi@1.11.1':
    resolution: {integrity: sha512-ppLRUgHVaGRWUx0R0Ut06Mjo9gBaBkg3v/8AxusGLhsIotbBLuRk51rAzqLC8gq6NyyAojEXglNjzf6R948DNw==}
    cpu: [arm]
    os: [android]

  '@unrs/resolver-binding-android-arm64@1.11.1':
    resolution: {integrity: sha512-lCxkVtb4wp1v+EoN+HjIG9cIIzPkX5OtM03pQYkG+U5O/wL53LC4QbIeazgiKqluGeVEeBlZahHalCaBvU1a2g==}
    cpu: [arm64]
    os: [android]

  '@unrs/resolver-binding-darwin-arm64@1.11.1':
    resolution: {integrity: sha512-gPVA1UjRu1Y/IsB/dQEsp2V1pm44Of6+LWvbLc9SDk1c2KhhDRDBUkQCYVWe6f26uJb3fOK8saWMgtX8IrMk3g==}
    cpu: [arm64]
    os: [darwin]

  '@unrs/resolver-binding-darwin-x64@1.11.1':
    resolution: {integrity: sha512-cFzP7rWKd3lZaCsDze07QX1SC24lO8mPty9vdP+YVa3MGdVgPmFc59317b2ioXtgCMKGiCLxJ4HQs62oz6GfRQ==}
    cpu: [x64]
    os: [darwin]

  '@unrs/resolver-binding-freebsd-x64@1.11.1':
    resolution: {integrity: sha512-fqtGgak3zX4DCB6PFpsH5+Kmt/8CIi4Bry4rb1ho6Av2QHTREM+47y282Uqiu3ZRF5IQioJQ5qWRV6jduA+iGw==}
    cpu: [x64]
    os: [freebsd]

  '@unrs/resolver-binding-linux-arm-gnueabihf@1.11.1':
    resolution: {integrity: sha512-u92mvlcYtp9MRKmP+ZvMmtPN34+/3lMHlyMj7wXJDeXxuM0Vgzz0+PPJNsro1m3IZPYChIkn944wW8TYgGKFHw==}
    cpu: [arm]
    os: [linux]

  '@unrs/resolver-binding-linux-arm-musleabihf@1.11.1':
    resolution: {integrity: sha512-cINaoY2z7LVCrfHkIcmvj7osTOtm6VVT16b5oQdS4beibX2SYBwgYLmqhBjA1t51CarSaBuX5YNsWLjsqfW5Cw==}
    cpu: [arm]
    os: [linux]

  '@unrs/resolver-binding-linux-arm64-gnu@1.11.1':
    resolution: {integrity: sha512-34gw7PjDGB9JgePJEmhEqBhWvCiiWCuXsL9hYphDF7crW7UgI05gyBAi6MF58uGcMOiOqSJ2ybEeCvHcq0BCmQ==}
    cpu: [arm64]
    os: [linux]
    libc: [glibc]

  '@unrs/resolver-binding-linux-arm64-musl@1.11.1':
    resolution: {integrity: sha512-RyMIx6Uf53hhOtJDIamSbTskA99sPHS96wxVE/bJtePJJtpdKGXO1wY90oRdXuYOGOTuqjT8ACccMc4K6QmT3w==}
    cpu: [arm64]
    os: [linux]
    libc: [musl]

  '@unrs/resolver-binding-linux-ppc64-gnu@1.11.1':
    resolution: {integrity: sha512-D8Vae74A4/a+mZH0FbOkFJL9DSK2R6TFPC9M+jCWYia/q2einCubX10pecpDiTmkJVUH+y8K3BZClycD8nCShA==}
    cpu: [ppc64]
    os: [linux]
    libc: [glibc]

  '@unrs/resolver-binding-linux-riscv64-gnu@1.11.1':
    resolution: {integrity: sha512-frxL4OrzOWVVsOc96+V3aqTIQl1O2TjgExV4EKgRY09AJ9leZpEg8Ak9phadbuX0BA4k8U5qtvMSQQGGmaJqcQ==}
    cpu: [riscv64]
    os: [linux]
    libc: [glibc]

  '@unrs/resolver-binding-linux-riscv64-musl@1.11.1':
    resolution: {integrity: sha512-mJ5vuDaIZ+l/acv01sHoXfpnyrNKOk/3aDoEdLO/Xtn9HuZlDD6jKxHlkN8ZhWyLJsRBxfv9GYM2utQ1SChKew==}
    cpu: [riscv64]
    os: [linux]
    libc: [musl]

  '@unrs/resolver-binding-linux-s390x-gnu@1.11.1':
    resolution: {integrity: sha512-kELo8ebBVtb9sA7rMe1Cph4QHreByhaZ2QEADd9NzIQsYNQpt9UkM9iqr2lhGr5afh885d/cB5QeTXSbZHTYPg==}
    cpu: [s390x]
    os: [linux]
    libc: [glibc]

  '@unrs/resolver-binding-linux-x64-gnu@1.11.1':
    resolution: {integrity: sha512-C3ZAHugKgovV5YvAMsxhq0gtXuwESUKc5MhEtjBpLoHPLYM+iuwSj3lflFwK3DPm68660rZ7G8BMcwSro7hD5w==}
    cpu: [x64]
    os: [linux]
    libc: [glibc]

  '@unrs/resolver-binding-linux-x64-musl@1.11.1':
    resolution: {integrity: sha512-rV0YSoyhK2nZ4vEswT/QwqzqQXw5I6CjoaYMOX0TqBlWhojUf8P94mvI7nuJTeaCkkds3QE4+zS8Ko+GdXuZtA==}
    cpu: [x64]
    os: [linux]
    libc: [musl]

  '@unrs/resolver-binding-wasm32-wasi@1.11.1':
    resolution: {integrity: sha512-5u4RkfxJm+Ng7IWgkzi3qrFOvLvQYnPBmjmZQ8+szTK/b31fQCnleNl1GgEt7nIsZRIf5PLhPwT0WM+q45x/UQ==}
    engines: {node: '>=14.0.0'}
    cpu: [wasm32]

  '@unrs/resolver-binding-win32-arm64-msvc@1.11.1':
    resolution: {integrity: sha512-nRcz5Il4ln0kMhfL8S3hLkxI85BXs3o8EYoattsJNdsX4YUU89iOkVn7g0VHSRxFuVMdM4Q1jEpIId1Ihim/Uw==}
    cpu: [arm64]
    os: [win32]

  '@unrs/resolver-binding-win32-ia32-msvc@1.11.1':
    resolution: {integrity: sha512-DCEI6t5i1NmAZp6pFonpD5m7i6aFrpofcp4LA2i8IIq60Jyo28hamKBxNrZcyOwVOZkgsRp9O2sXWBWP8MnvIQ==}
    cpu: [ia32]
    os: [win32]

  '@unrs/resolver-binding-win32-x64-msvc@1.11.1':
    resolution: {integrity: sha512-lrW200hZdbfRtztbygyaq/6jP6AKE8qQN2KvPcJ+x7wiD038YtnYtZ82IMNJ69GJibV7bwL3y9FgK+5w/pYt6g==}
    cpu: [x64]
    os: [win32]

  '@vercel/nft@1.5.0':
    resolution: {integrity: sha512-IWTDeIoWhQ7ZtRO/JRKH+jhmeQvZYhtGPmzw/QGDY+wDCQqfm25P9yIdoAFagu4fWsK4IwZXDFIjrmp5rRm/sA==}
    engines: {node: '>=20'}
    hasBin: true

  '@vitejs/plugin-vue-jsx@5.1.5':
    resolution: {integrity: sha512-jIAsvHOEtWpslLOI2MeElGFxH7M8pM83BU/Tor4RLyiwH0FM4nUW3xdvbw20EeU9wc5IspQwMq225K3CMnJEpA==}
    engines: {node: ^20.19.0 || >=22.12.0}
    peerDependencies:
      vite: ^5.0.0 || ^6.0.0 || ^7.0.0 || ^8.0.0
      vue: ^3.0.0

  '@vitejs/plugin-vue@6.0.6':
    resolution: {integrity: sha512-u9HHgfrq3AjXlysn0eINFnWQOJQLO9WN6VprZ8FXl7A2bYisv3Hui9Ij+7QZ41F/WYWarHjwBbXtD7dKg3uxbg==}
    engines: {node: ^20.19.0 || >=22.12.0}
    peerDependencies:
      vite: ^5.0.0 || ^6.0.0 || ^7.0.0 || ^8.0.0
      vue: ^3.2.25

  '@volar/language-core@2.4.28':
    resolution: {integrity: sha512-w4qhIJ8ZSitgLAkVay6AbcnC7gP3glYM3fYwKV3srj8m494E3xtrCv6E+bWviiK/8hs6e6t1ij1s2Endql7vzQ==}

  '@volar/source-map@2.4.28':
    resolution: {integrity: sha512-yX2BDBqJkRXfKw8my8VarTyjv48QwxdJtvRgUpNE5erCsgEUdI2DsLbpa+rOQVAJYshY99szEcRDmyHbF10ggQ==}

  '@volar/typescript@2.4.28':
    resolution: {integrity: sha512-Ja6yvWrbis2QtN4ClAKreeUZPVYMARDYZl9LMEv1iQ1QdepB6wn0jTRxA9MftYmYa4DQ4k/DaSZpFPUfxl8giw==}

  '@vue-macros/common@3.1.2':
    resolution: {integrity: sha512-h9t4ArDdniO9ekYHAD95t9AZcAbb19lEGK+26iAjUODOIJKmObDNBSe4+6ELQAA3vtYiFPPBtHh7+cQCKi3Dng==}
    engines: {node: '>=20.19.0'}
    peerDependencies:
      vue: ^2.7.0 || ^3.2.25
    peerDependenciesMeta:
      vue:
        optional: true

  '@vue/babel-helper-vue-transform-on@2.0.1':
    resolution: {integrity: sha512-uZ66EaFbnnZSYqYEyplWvn46GhZ1KuYSThdT68p+am7MgBNbQ3hphTL9L+xSIsWkdktwhPYLwPgVWqo96jDdRA==}

  '@vue/babel-plugin-jsx@2.0.1':
    resolution: {integrity: sha512-a8CaLQjD/s4PVdhrLD/zT574ZNPnZBOY+IhdtKWRB4HRZ0I2tXBi5ne7d9eCfaYwp5gU5+4KIyFTV1W1YL9xZA==}
    peerDependencies:
      '@babel/core': ^7.0.0-0
    peerDependenciesMeta:
      '@babel/core':
        optional: true

  '@vue/babel-plugin-resolve-type@2.0.1':
    resolution: {integrity: sha512-ybwgIuRGRRBhOU37GImDoWQoz+TlSqap65qVI6iwg/J7FfLTLmMf97TS7xQH9I7Qtr/gp161kYVdhr1ZMraSYQ==}
    peerDependencies:
      '@babel/core': ^7.0.0-0

  '@vue/compiler-core@3.5.33':
    resolution: {integrity: sha512-3PZLQwFw4Za3TC8t0FvTy3wI16Kt+pmwcgNZca4Pj9iWL2E72a/gZlpBtAJvEdDMdCxdG/qq0C7PN0bsJuv0Rw==}

  '@vue/compiler-dom@3.5.33':
    resolution: {integrity: sha512-PXq0yrfCLzzL07rbXO4awtXY1Z06LG2eu6Adg3RJFa/j3Cii217XxxLXG22N330gw7GmALCY0Z8RgXEviwgpjA==}

  '@vue/compiler-sfc@3.5.33':
    resolution: {integrity: sha512-UTUvRO9cY+rROrx/pvN9P5Z7FgA6QGfokUCfhQE4EnmUj3rVnK+CHI0LsEO1pg+I7//iRYMUfcNcCPe7tg0CoA==}

  '@vue/compiler-ssr@3.5.33':
    resolution: {integrity: sha512-IErjYdnj1qIupG5xxiVIYiiRvDhGWV4zuh/RCrwfYpuL+HWQzeU6lCk/nF9r7olWMnjKxCAkOctT2qFWFkzb1A==}

  '@vue/devtools-api@8.1.0':
    resolution: {integrity: sha512-O44X57jjkLKbLEc4OgL/6fEPOOanRJU8kYpCE8qfKlV96RQZcdzrcLI5mxMuVRUeXhHKIHGhCpHacyCk0HyO4w==}

  '@vue/devtools-core@8.1.0':
    resolution: {integrity: sha512-LvD1VgDpoHmYL00IgKRLKktF6SsPAb0yaV8wB8q2jRwsAWvqhS8+vsMLEGKNs7uoKyymXhT92dhxgf/wir6YGQ==}
    peerDependencies:
      vue: ^3.0.0

  '@vue/devtools-kit@8.1.0':
    resolution: {integrity: sha512-/NZlS4WtGIB54DA/z10gzk+n/V7zaqSzYZOVlg2CfdnpIKdB61bd7JDIMxf/zrtX41zod8E2/bbEBoW/d7x70Q==}

  '@vue/devtools-shared@8.1.0':
    resolution: {integrity: sha512-h8uCb4Qs8UT8VdTT5yjY6tOJ//qH7EpxToixR0xqejR55t5OdISIg7AJ7eBkhBs8iu1qG5gY3QQNN1DF1EelAA==}

  '@vue/language-core@3.2.5':
    resolution: {integrity: sha512-d3OIxN/+KRedeM5wQ6H6NIpwS3P5gC9nmyaHgBk+rO6dIsjY+tOh4UlPpiZbAh3YtLdCGEX4M16RmsBqPmJV+g==}

  '@vue/language-core@3.2.8':
    resolution: {integrity: sha512-9OiSPQFiAAWNVnXb0d2dcTmcKnFQamhuNES6ayyISrb/mwPWVgoGdAqSfCWqKhQpa3D5gDTcYD+w7ObiheZ81g==}

  '@vue/reactivity@3.5.33':
    resolution: {integrity: sha512-p8UfIqyIhb0rYGlSgSBV+lPhF2iUSBcRy7enhTmPqKWadHy9kcOFYF1AejYBP9P+avnd3OBbD49DU4pLWX/94A==}

  '@vue/runtime-core@3.5.33':
    resolution: {integrity: sha512-UpFF45RI9//a7rvq7RdOQblb4tup7hHG9QsmIrxkFQLzQ7R8/iNQ5LE15NhLZ1/WcHMU2b47u6P33CPUelHyIQ==}

  '@vue/runtime-dom@3.5.33':
    resolution: {integrity: sha512-IOxMsAOwquhfITgmOgaPYl7/j8gKUxUFoflRc+u4LxyD3+783xne8vNta1PONVCvCV9A0w7hkyEepINDqfO0tw==}

  '@vue/server-renderer@3.5.33':
    resolution: {integrity: sha512-0xylq/8/h44lVG0pZFknv1XIdEgymq2E9n59uTWJBG+dIgiT0TMCSsxrN7nO16Z0MU0MPjFcguBbZV8Itk52Hw==}
    peerDependencies:
      vue: 3.5.33

  '@vue/shared@3.5.33':
    resolution: {integrity: sha512-5vR2QIlmaLG77Ygd4pMP6+SGQ5yox9VhtnbDWTy9DzMzdmeLxZ1QqxrywEZ9sa1AVubfIJyaCG3ytyWU81ufcQ==}

  '@vueuse/core@10.11.1':
    resolution: {integrity: sha512-guoy26JQktXPcz+0n3GukWIy/JDNKti9v6VEMu6kV2sYBsWuGiTU8OWdg+ADfUbHg3/3DlqySDe7JmdHrktiww==}

  '@vueuse/core@14.2.1':
    resolution: {integrity: sha512-3vwDzV+GDUNpdegRY6kzpLm4Igptq+GA0QkJ3W61Iv27YWwW/ufSlOfgQIpN6FZRMG0mkaz4gglJRtq5SeJyIQ==}
    peerDependencies:
      vue: ^3.5.0

  '@vueuse/core@14.3.0':
    resolution: {integrity: sha512-aHfz47g0ZhMtTVHmIzMVpJy8ePhhOy68GY5bv110+5DVtZ+W7BsOx+m61UNQqfrWyPztIHIanWa3E2tib3NFIw==}
    peerDependencies:
      vue: ^3.5.0

  '@vueuse/integrations@14.2.1':
    resolution: {integrity: sha512-2LIUpBi/67PoXJGqSDQUF0pgQWpNHh7beiA+KG2AbybcNm+pTGWT6oPGlBgUoDWmYwfeQqM/uzOHqcILpKL7nA==}
    peerDependencies:
      async-validator: ^4
      axios: ^1
      change-case: ^5
      drauu: ^0.4
      focus-trap: ^7 || ^8
      fuse.js: ^7
      idb-keyval: ^6
      jwt-decode: ^4
      nprogress: ^0.2
      qrcode: ^1.5
      sortablejs: ^1
      universal-cookie: ^7 || ^8
      vue: ^3.5.0
    peerDependenciesMeta:
      async-validator:
        optional: true
      axios:
        optional: true
      change-case:
        optional: true
      drauu:
        optional: true
      focus-trap:
        optional: true
      fuse.js:
        optional: true
      idb-keyval:
        optional: true
      jwt-decode:
        optional: true
      nprogress:
        optional: true
      qrcode:
        optional: true
      sortablejs:
        optional: true
      universal-cookie:
        optional: true

  '@vueuse/metadata@10.11.1':
    resolution: {integrity: sha512-IGa5FXd003Ug1qAZmyE8wF3sJ81xGLSqTqtQ6jaVfkeZ4i5kS2mwQF61yhVqojRnenVew5PldLyRgvdl4YYuSw==}

  '@vueuse/metadata@14.2.1':
    resolution: {integrity: sha512-1ButlVtj5Sb/HDtIy1HFr1VqCP4G6Ypqt5MAo0lCgjokrk2mvQKsK2uuy0vqu/Ks+sHfuHo0B9Y9jn9xKdjZsw==}

  '@vueuse/metadata@14.3.0':
    resolution: {integrity: sha512-BwxmbAzwAVF50+MW57GXOUEV61nFBGnlBvrTqj49PqWJu3uw7hdu72ztXeZ33RdZtDY6kO+bfCAE1PCn88Tktw==}

  '@vueuse/shared@10.11.1':
    resolution: {integrity: sha512-LHpC8711VFZlDaYUXEBbFBCQ7GS3dVU9mjOhhMhXP6txTV4EhYQg/KGnQuvt/sPAtoUKq7VVUnL6mVtFoL42sA==}

  '@vueuse/shared@14.2.1':
    resolution: {integrity: sha512-shTJncjV9JTI4oVNyF1FQonetYAiTBd+Qj7cY89SWbXSkx7gyhrgtEdF2ZAVWS1S3SHlaROO6F2IesJxQEkZBw==}
    peerDependencies:
      vue: ^3.5.0

  '@vueuse/shared@14.3.0':
    resolution: {integrity: sha512-bZpge9eSXwa4ToSiqJ7j6KRwhAsneMFoSz3LMWKQDkqimm3D/tbFlrklrs/IOqC8tEcYmXQZJ6N0UrjhBirVCg==}
    peerDependencies:
      vue: ^3.5.0

  '@webcontainer/env@1.1.1':
    resolution: {integrity: sha512-6aN99yL695Hi9SuIk1oC88l9o0gmxL1nGWWQ/kNy81HigJ0FoaoTXpytCj6ItzgyCEwA9kF1wixsTuv5cjsgng==}

  abbrev@3.0.1:
    resolution: {integrity: sha512-AO2ac6pjRB3SJmGJo+v5/aK6Omggp6fsLrs6wN9bd35ulu4cCwaAU9+7ZhXjeqHVkaHThLuzH0nZr0YpCDhygg==}
    engines: {node: ^18.17.0 || >=20.5.0}

  abort-controller@3.0.0:
    resolution: {integrity: sha512-h8lQ8tacZYnR3vNQTgibj+tODHI5/+l06Au2Pcriv/Gmet0eaj4TwWH41sO9wnHDiQsEj19q0drzdWdeAHtweg==}
    engines: {node: '>=6.5'}

  accepts@2.0.0:
    resolution: {integrity: sha512-5cvg6CtKwfgdmVqY1WIiXKc3Q1bkRqGLi+2W/6ao+6Y7gu/RCwRuAhGEzh5B4KlszSuTLgZYuqFqo5bImjNKng==}
    engines: {node: '>= 0.6'}

  acorn-import-attributes@1.9.5:
    resolution: {integrity: sha512-n02Vykv5uA3eHGM/Z2dQrcD56kL8TyDb2p1+0P83PClMnC/nc+anbQRhIOWnSq4Ke/KvDPrY3C9hDtC/A3eHnQ==}
    peerDependencies:
      acorn: ^8

  acorn-jsx@5.3.2:
    resolution: {integrity: sha512-rq9s+JNhf0IChjtDXxllJ7g41oZk5SlXtp0LHwyA5cejwn7vKmKp4pPri6YEePv2PU65sAsegbXtIinmDFDXgQ==}
    peerDependencies:
      acorn: ^6.0.0 || ^7.0.0 || ^8.0.0

  acorn@8.16.0:
    resolution: {integrity: sha512-UVJyE9MttOsBQIDKw1skb9nAwQuR5wuGD3+82K6JgJlm/Y+KI92oNsMNGZCYdDsVtRHSak0pcV5Dno5+4jh9sw==}
    engines: {node: '>=0.4.0'}
    hasBin: true

  agent-base@7.1.4:
    resolution: {integrity: sha512-MnA+YT8fwfJPgBx3m60MNqakm30XOkyIoH1y6huTQvC0PwZG7ki8NacLBcrPbNoo8vEZy7Jpuk7+jMO+CUovTQ==}
    engines: {node: '>= 14'}

  ajv-formats@3.0.1:
    resolution: {integrity: sha512-8iUql50EUR+uUcdRQ3HDqa6EVyo3docL8g5WJ3FNcWmu62IbkGUue/pEyLBW8VGKKucTPgqeks4fIU1DA4yowQ==}
    peerDependencies:
      ajv: ^8.0.0
    peerDependenciesMeta:
      ajv:
        optional: true

  ajv@6.14.0:
    resolution: {integrity: sha512-IWrosm/yrn43eiKqkfkHis7QioDleaXQHdDVPKg0FSwwd/DuvyX79TZnFOnYpB7dcsFAMmtFztZuXPDvSePkFw==}

  ajv@8.18.0:
    resolution: {integrity: sha512-PlXPeEWMXMZ7sPYOHqmDyCJzcfNrUr3fGNKtezX14ykXOEIvyK81d+qydx89KY5O71FKMPaQ2vBfBFI5NHR63A==}

  alien-signals@3.1.2:
    resolution: {integrity: sha512-d9dYqZTS90WLiU0I5c6DHj/HcKkF8ZyGN3G5x8wSbslulz70KOxaqCT0hQCo9KOyhVqzqGojvNdJXoTumZOtcw==}

  ansi-regex@5.0.1:
    resolution: {integrity: sha512-quJQXlTSUGL2LH9SUXo8VwsY4soanhgo6LNSm84E1LBcE8s3O0wpdiRzyR9z/ZZJMlMWv37qOOb9pdJlMUEKFQ==}
    engines: {node: '>=8'}

  ansi-regex@6.2.2:
    resolution: {integrity: sha512-Bq3SmSpyFHaWjPk8If9yc6svM8c56dB5BAtW4Qbw5jHTwwXXcTLoRMkpDJp6VL0XzlWaCHTXrkFURMYmD0sLqg==}
    engines: {node: '>=12'}

  ansi-styles@4.3.0:
    resolution: {integrity: sha512-zbB9rCJAT1rbjiVDb2hqKFHNYLxgtk8NURxZ3IZwD3F6NtxbXZQCnnSi1Lkx+IDohdPlFp222wVALIheZJQSEg==}
    engines: {node: '>=8'}

  ansi-styles@6.2.3:
    resolution: {integrity: sha512-4Dj6M28JB+oAH8kFkTLUo+a2jwOFkuqb3yucU0CANcRRUbxS0cP0nZYCGjcc3BNXwRIsUVmDGgzawme7zvJHvg==}
    engines: {node: '>=12'}

  ansis@4.2.0:
    resolution: {integrity: sha512-HqZ5rWlFjGiV0tDm3UxxgNRqsOTniqoKZu0pIAfh7TZQMGuZK+hH0drySty0si0QXj1ieop4+SkSfPZBPPkHig==}
    engines: {node: '>=14'}

  anymatch@3.1.3:
    resolution: {integrity: sha512-KMReFUr0B4t+D+OBkjR3KYqvocp2XaSzO55UcB6mgQMd3KbcE+mWTyvVV7D/zsdEbNnV6acZUutkiHQXvTr1Rw==}
    engines: {node: '>= 8'}

  archiver-utils@5.0.2:
    resolution: {integrity: sha512-wuLJMmIBQYCsGZgYLTy5FIB2pF6Lfb6cXMSF8Qywwk3t20zWnAi7zLcQFdKQmIB8wyZpY5ER38x08GbwtR2cLA==}
    engines: {node: '>= 14'}

  archiver@7.0.1:
    resolution: {integrity: sha512-ZcbTaIqJOfCc03QwD468Unz/5Ir8ATtvAHsK+FdXbDIbGfihqh9mrvdcYunQzqn4HrvWWaFyaxJhGZagaJJpPQ==}
    engines: {node: '>= 14'}

  are-docs-informative@0.0.2:
    resolution: {integrity: sha512-ixiS0nLNNG5jNQzgZJNoUpBKdo9yTYZMGJ+QgT2jmjR7G7+QHRCc4v6LQ3NgE7EBJq+o0ams3waJwkrlBom8Ig==}
    engines: {node: '>=14'}

  argparse@2.0.1:
    resolution: {integrity: sha512-8+9WqebbFzpX9OR+Wa6O29asIogeRMzcGtAINdpMHHyAg10f05aSFVBbcEqGf/PXw1EjAZ+q2/bEBg3DvurK3Q==}

  aria-hidden@1.2.6:
    resolution: {integrity: sha512-ik3ZgC9dY/lYVVM++OISsaYDeg1tb0VtP5uL3ouh1koGOaUMDPpbFIei4JkFimWUFPn90sbMNMXQAIVOlnYKJA==}
    engines: {node: '>=10'}

  ast-kit@2.2.0:
    resolution: {integrity: sha512-m1Q/RaVOnTp9JxPX+F+Zn7IcLYMzM8kZofDImfsKZd8MbR+ikdOzTeztStWqfrqIxZnYWryyI9ePm3NGjnZgGw==}
    engines: {node: '>=20.19.0'}

  ast-walker-scope@0.8.3:
    resolution: {integrity: sha512-cbdCP0PGOBq0ASG+sjnKIoYkWMKhhz+F/h9pRexUdX2Hd38+WOlBkRKlqkGOSm0YQpcFMQBJeK4WspUAkwsEdg==}
    engines: {node: '>=20.19.0'}

  async-lock@1.4.1:
    resolution: {integrity: sha512-Az2ZTpuytrtqENulXwO3GGv1Bztugx6TT37NIo7imr/Qo0gsYiGtSdBa2B6fsXhTpVZDNfu1Qn3pk531e3q+nQ==}

  async-sema@3.1.1:
    resolution: {integrity: sha512-tLRNUXati5MFePdAk8dw7Qt7DpxPB60ofAgn8WRhW6a2rcimZnYBP9oxHiv0OHy+Wz7kPMG+t4LGdt31+4EmGg==}

  async@3.2.6:
    resolution: {integrity: sha512-htCUDlxyyCLMgaM3xXg0C0LW2xqfuQ6p05pCEIsXuyQ+a1koYKTuBMzRNwmybfLgvJDMd0r1LTn4+E0Ti6C2AA==}

  autoprefixer@10.5.0:
    resolution: {integrity: sha512-FMhOoZV4+qR6aTUALKX2rEqGG+oyATvwBt9IIzVR5rMa2HRWPkxf+P+PAJLD1I/H5/II+HuZcBJYEFBpq39ong==}
    engines: {node: ^10 || ^12 || >=14}
    hasBin: true
    peerDependencies:
      postcss: ^8.1.0

  available-typed-arrays@1.0.7:
    resolution: {integrity: sha512-wvUjBtSGN7+7SjNpq/9M2Tg350UZD3q62IFZLbRAR1bSMlCo1ZaeW+BJ+D090e4hIIZLBcTDWe4Mh4jvUDajzQ==}
    engines: {node: '>= 0.4'}

  b4a@1.8.0:
    resolution: {integrity: sha512-qRuSmNSkGQaHwNbM7J78Wwy+ghLEYF1zNrSeMxj4Kgw6y33O3mXcQ6Ie9fRvfU/YnxWkOchPXbaLb73TkIsfdg==}
    peerDependencies:
      react-native-b4a: '*'
    peerDependenciesMeta:
      react-native-b4a:
        optional: true

  bail@2.0.2:
    resolution: {integrity: sha512-0xO6mYd7JB2YesxDKplafRpsiOzPt9V02ddPCLbY1xYGPOX24NTyN50qnUxgCPcSoYMhKpAuBTjQoRZCAkUDRw==}

  balanced-match@1.0.2:
    resolution: {integrity: sha512-3oSeUO0TMV67hN1AmbXsK4yaqU7tjiHlbxRDZOpH0KW9+CeX4bRAaX0Anxt0tx2MrpRpWwQaPwIlISEJhYU5Pw==}

  balanced-match@4.0.4:
    resolution: {integrity: sha512-BLrgEcRTwX2o6gGxGOCNyMvGSp35YofuYzw9h1IMTRmKqttAZZVU67bdb9Pr2vUHA8+j3i2tJfjO6C6+4myGTA==}
    engines: {node: 18 || 20 || >=22}

  bare-events@2.8.2:
    resolution: {integrity: sha512-riJjyv1/mHLIPX4RwiK+oW9/4c3TEUeORHKefKAKnZ5kyslbN+HXowtbaVEqt4IMUB7OXlfixcs6gsFeo/jhiQ==}
    peerDependencies:
      bare-abort-controller: '*'
    peerDependenciesMeta:
      bare-abort-controller:
        optional: true

  bare-fs@4.5.5:
    resolution: {integrity: sha512-XvwYM6VZqKoqDll8BmSww5luA5eflDzY0uEFfBJtFKe4PAAtxBjU3YIxzIBzhyaEQBy1VXEQBto4cpN5RZJw+w==}
    engines: {bare: '>=1.16.0'}
    peerDependencies:
      bare-buffer: '*'
    peerDependenciesMeta:
      bare-buffer:
        optional: true

  bare-os@3.8.0:
    resolution: {integrity: sha512-Dc9/SlwfxkXIGYhvMQNUtKaXCaGkZYGcd1vuNUUADVqzu4/vQfvnMkYYOUnt2VwQ2AqKr/8qAVFRtwETljgeFg==}
    engines: {bare: '>=1.14.0'}

  bare-path@3.0.0:
    resolution: {integrity: sha512-tyfW2cQcB5NN8Saijrhqn0Zh7AnFNsnczRcuWODH0eYAXBsJ5gVxAUuNr7tsHSC6IZ77cA0SitzT+s47kot8Mw==}

  bare-stream@2.8.1:
    resolution: {integrity: sha512-bSeR8RfvbRwDpD7HWZvn8M3uYNDrk7m9DQjYOFkENZlXW8Ju/MPaqUPQq5LqJ3kyjEm07siTaAQ7wBKCU59oHg==}
    peerDependencies:
      bare-buffer: '*'
      bare-events: '*'
    peerDependenciesMeta:
      bare-buffer:
        optional: true
      bare-events:
        optional: true

  bare-url@2.3.2:
    resolution: {integrity: sha512-ZMq4gd9ngV5aTMa5p9+UfY0b3skwhHELaDkhEHetMdX0LRkW9kzaym4oo/Eh+Ghm0CCDuMTsRIGM/ytUc1ZYmw==}

  base64-js@1.5.1:
    resolution: {integrity: sha512-AKpaYlHn8t4SVbOHCy+b5+KKgvR4vrsD8vbvrbiQJps7fKDTkjkDry6ji0rUJjC0kzbNePLwzxq8iypo41qeWA==}

  baseline-browser-mapping@2.10.27:
    resolution: {integrity: sha512-zEs/ufmZoUd7WftKpKyXaT6RFxpQ5Qm9xytKRHvJfxFV9DFJkZph9RvJ1LcOUi0Z1ZVijMte65JbILeV+8QQEA==}
    engines: {node: '>=6.0.0'}
    hasBin: true

  better-sqlite3@12.9.0:
    resolution: {integrity: sha512-wqUv4Gm3toFpHDQmaKD4QhZm3g1DjUBI0yzS4UBl6lElUmXFYdTQmmEDpAFa5o8FiFiymURypEnfVHzILKaxqQ==}
    engines: {node: 20.x || 22.x || 23.x || 24.x || 25.x}

  bindings@1.5.0:
    resolution: {integrity: sha512-p2q/t/mhvuOj/UeLlV6566GD/guowlr0hHxClI0W9m7MWYkL1F0hLo+0Aexs9HSPCtR1SXQ0TD3MMKrXZajbiQ==}

  birpc@2.9.0:
    resolution: {integrity: sha512-KrayHS5pBi69Xi9JmvoqrIgYGDkD6mcSe/i6YKi3w5kekCLzrX4+nawcXqrj2tIp50Kw/mT/s3p+GVK0A0sKxw==}

  birpc@4.0.0:
    resolution: {integrity: sha512-LShSxJP0KTmd101b6DRyGBj57LZxSDYWKitQNW/mi8GRMvZb078Uf9+pveax1DrVL89vm7mWe+TovdI/UDOuPw==}

  bl@4.1.0:
    resolution: {integrity: sha512-1W07cM9gS6DcLperZfFSj+bWLtaPGSOHWhPiGzXmvVJbRLdG82sH/Kn8EtW1VqWVA54AKf2h5k5BbnIbwF3h6w==}

  body-parser@2.2.2:
    resolution: {integrity: sha512-oP5VkATKlNwcgvxi0vM0p/D3n2C3EReYVX+DNYs5TjZFn/oQt2j+4sVJtSMr18pdRr8wjTcBl6LoV+FUwzPmNA==}
    engines: {node: '>=18'}

  boolbase@1.0.0:
    resolution: {integrity: sha512-JZOSA7Mo9sNGB8+UjSgzdLtokWAky1zbztM3WRLCbZ70/3cTANmQmOdR7y2g+J0e2WXywy1yS468tY+IruqEww==}

  brace-expansion@2.0.2:
    resolution: {integrity: sha512-Jt0vHyM+jmUBqojB7E1NIYadt0vI0Qxjxd2TErW94wDz+E2LAm5vKMXXwg6ZZBTHPuUlDgQHKXvjGBdfcF1ZDQ==}

  brace-expansion@5.0.4:
    resolution: {integrity: sha512-h+DEnpVvxmfVefa4jFbCf5HdH5YMDXRsmKflpf1pILZWRFlTbJpxeU55nJl4Smt5HQaGzg1o6RHFPJaOqnmBDg==}
    engines: {node: 18 || 20 || >=22}

  braces@3.0.3:
    resolution: {integrity: sha512-yQbXgO/OSZVD2IsiLlro+7Hf6Q18EJrKSEsdoMzKePKXct3gvD8oLcOQdIzGupr5Fj+EDe8gO/lxc1BzfMpxvA==}
    engines: {node: '>=8'}

  browserslist@4.28.2:
    resolution: {integrity: sha512-48xSriZYYg+8qXna9kwqjIVzuQxi+KYWp2+5nCYnYKPTr0LvD89Jqk2Or5ogxz0NUMfIjhh2lIUX/LyX9B4oIg==}
    engines: {node: ^6 || ^7 || ^8 || ^9 || ^10 || ^11 || ^12 || >=13.7}
    hasBin: true

  buffer-crc32@1.0.0:
    resolution: {integrity: sha512-Db1SbgBS/fg/392AblrMJk97KggmvYhr4pB5ZIMTWtaivCPMWLkmb7m21cJvpvgK+J3nsU2CmmixNBZx4vFj/w==}
    engines: {node: '>=8.0.0'}

  buffer-from@1.1.2:
    resolution: {integrity: sha512-E+XQCRwSbaaiChtv6k6Dwgc+bx+Bs6vuKJHHl5kox/BaKbhiXzqQOwK4cO22yElGp2OCmjwVhT3HmxgyPGnJfQ==}

  buffer@5.7.1:
    resolution: {integrity: sha512-EHcyIPBQ4BSGlvjB16k5KgAJ27CIsHY/2JBmCRReo48y9rQ3MaUzWX3KVlBa4U7MyX02HdVj0K7C3WaB3ju7FQ==}

  buffer@6.0.3:
    resolution: {integrity: sha512-FTiCpNxtwiZZHEZbcbTIcZjERVICn9yq/pDFkTl95/AxzD1naBctN7YO68riM/gLSDY7sdrMby8hofADYuuqOA==}

  builtin-modules@5.0.0:
    resolution: {integrity: sha512-bkXY9WsVpY7CvMhKSR6pZilZu9Ln5WDrKVBUXf2S443etkmEO4V58heTecXcUIsNsi4Rx8JUO4NfX1IcQl4deg==}
    engines: {node: '>=18.20'}

  bundle-name@4.1.0:
    resolution: {integrity: sha512-tjwM5exMg6BGRI+kNmTntNsvdZS1X8BFYS6tnJ2hdH0kVxM6/eVZ2xy+FqStSWvYmtfFMDLIxurorHwDKfDz5Q==}
    engines: {node: '>=18'}

  bundle-require@5.1.0:
    resolution: {integrity: sha512-3WrrOuZiyaaZPWiEt4G3+IffISVC9HYlWueJEBWED4ZH4aIAC2PnkdnuRrR94M+w6yGWn4AglWtJtBI8YqvgoA==}
    engines: {node: ^12.20.0 || ^14.13.1 || >=16.0.0}
    peerDependencies:
      esbuild: '>=0.18'

  bytes@3.1.2:
    resolution: {integrity: sha512-/Nf7TyzTx6S3yRJObOAV7956r8cr2+Oj8AC5dt8wSP3BQAoeX58NoHyCU8P8zGkNXStjTSi6fzO6F0pBdcYbEg==}
    engines: {node: '>= 0.8'}

  c12@3.3.4:
    resolution: {integrity: sha512-cM0ApFQSBXuourJejzwv/AuPRvAxordTyParRVcHjjtXirtkzM0uK2L9TTn9s0cXZbG7E55jCivRQzoxYmRAlA==}
    peerDependencies:
      magicast: '*'
    peerDependenciesMeta:
      magicast:
        optional: true

  cac@6.7.14:
    resolution: {integrity: sha512-b6Ilus+c3RrdDk+JhLKUAQfzzgLEPy6wcXqS7f/xe1EETvsDP6GORG7SFuOs6cID5YkqchW/LXZbX5bc8j7ZcQ==}
    engines: {node: '>=8'}

  cac@7.0.0:
    resolution: {integrity: sha512-tixWYgm5ZoOD+3g6UTea91eow5z6AAHaho3g0V9CNSNb45gM8SmflpAc+GRd1InC4AqN/07Unrgp56Y94N9hJQ==}
    engines: {node: '>=20.19.0'}

  call-bind-apply-helpers@1.0.2:
    resolution: {integrity: sha512-Sp1ablJ0ivDkSzjcaJdxEunN5/XvksFJ2sMBFfq6x0ryhQV/2b/KwFe21cMpmHtPOSij8K99/wSfoEuTObmuMQ==}
    engines: {node: '>= 0.4'}

  call-bind@1.0.8:
    resolution: {integrity: sha512-oKlSFMcMwpUg2ednkhQ454wfWiU/ul3CkJe/PEHcTKuiX6RpbehUiFMXu13HalGZxfUwCQzZG747YXBn1im9ww==}
    engines: {node: '>= 0.4'}

  call-bound@1.0.4:
    resolution: {integrity: sha512-+ys997U96po4Kx/ABpBCqhA9EuxJaQWDQg7295H4hBphv3IZg0boBKuwYpt4YXp6MZ5AmZQnU/tyMTlRpaSejg==}
    engines: {node: '>= 0.4'}

  caniuse-api@3.0.0:
    resolution: {integrity: sha512-bsTwuIg/BZZK/vreVTYYbSWoe2F+71P7K5QGEX+pT250DZbfU1MQ5prOKpPR+LL6uWKK3KMwMCAS74QB3Um1uw==}
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
